sonyc-project/SONYC-Home/Hardware/Design Files/STEP files/Gasket rev2.STEP

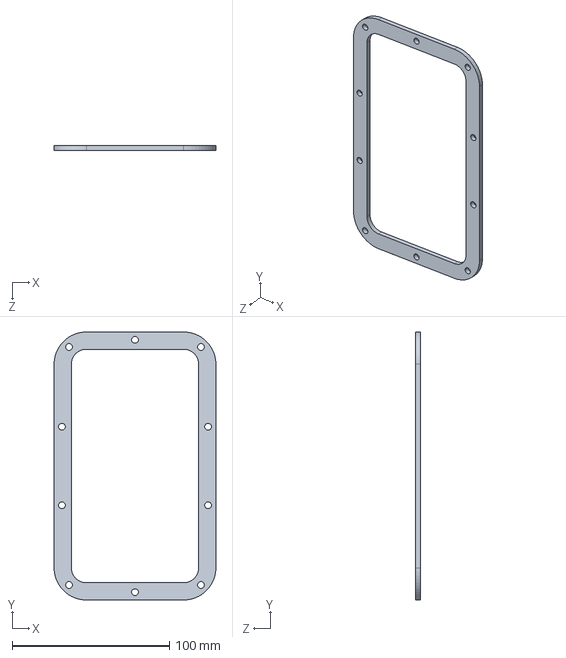
[picture p9: CAD file, 2023-06-01]
Hardware/Design Files/STEP files/Gasket rev2.STEP
102.9 x 170.4 x 3.17 mm
