sonyc-project/SONYC-Home/Hardware/Design Files/Solidworks CAD/SONYC-SW-database/SHR-05V-S-B.sldprt

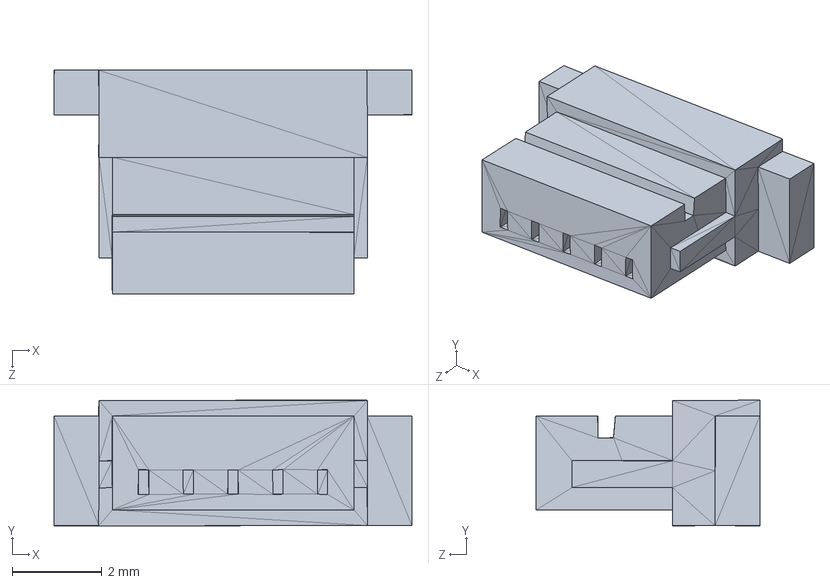
[picture p10: CAD file, 2023-06-01]
Hardware/Design Files/Solidworks CAD/SONYC-SW-database/SHR-05V-S-B.sldprt
8.00 x 2.81 x 5.01 mm
