sonyc-project/SONYC-Home/Hardware/Design Files/Solidworks CAD/SONYC-SW-database/Back-Plate.SLDPRT

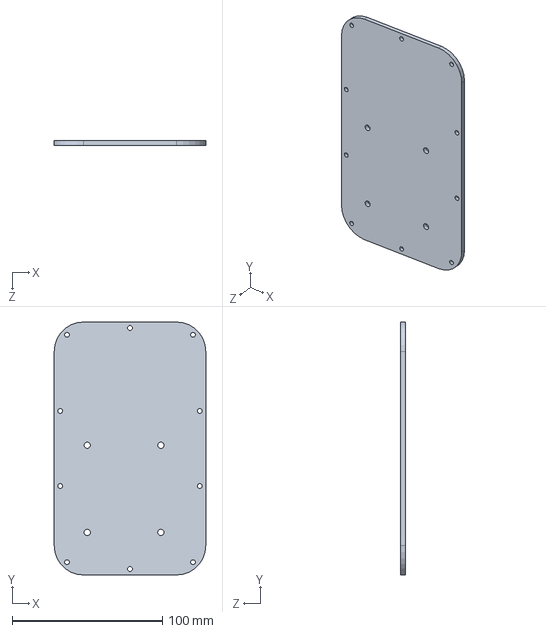
[picture p11: CAD file, 2023-06-01]
Hardware/Design Files/Solidworks CAD/SONYC-SW-database/Back-Plate.SLDPRT
100.9 x 168.4 x 3.00 mm
