sonyc-project/SONYC-Home/Hardware/Design Files/Solidworks CAD/SONYC-SW-database/cicoil-cable.SLDPRT

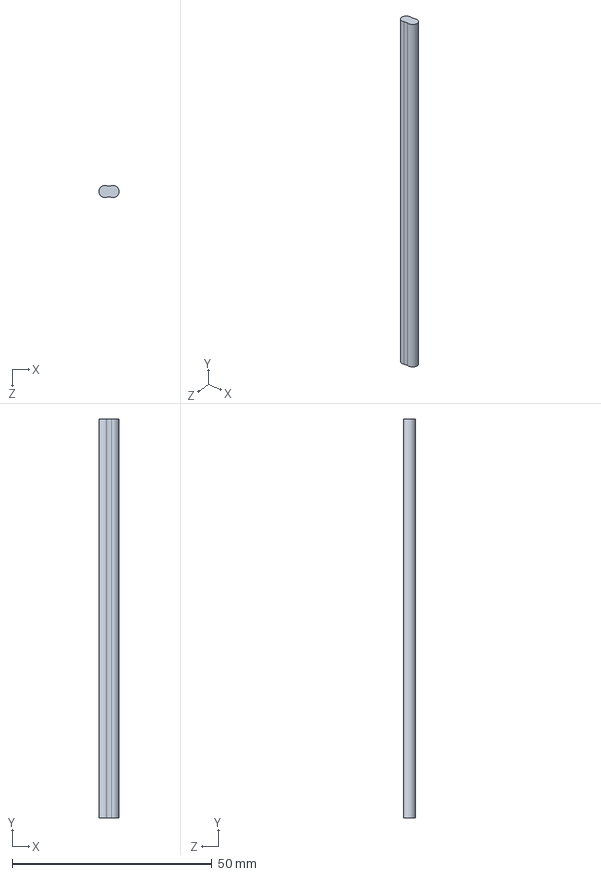
[picture p12: CAD file, 2023-06-01]
Hardware/Design Files/Solidworks CAD/SONYC-SW-database/cicoil-cable.SLDPRT
5.06 x 100.0 x 3.05 mm
