sonyc-project/SONYC-Home/Hardware/Design Files/Solidworks CAD/SONYC-SW-database/SONYC-Heat-sink-block.SLDPRT

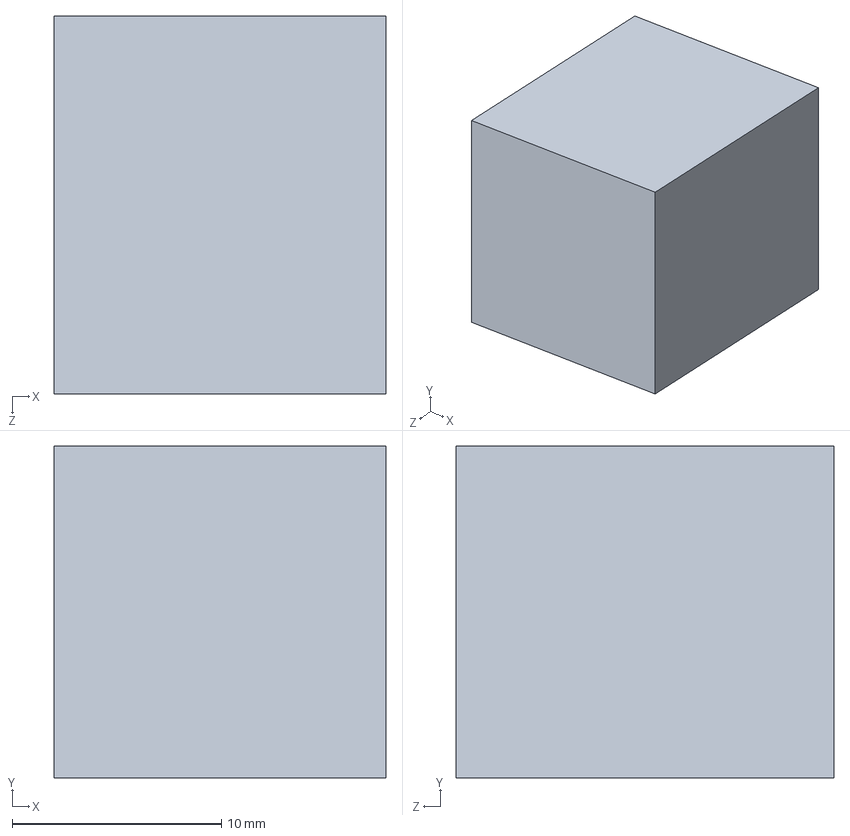
[picture p13: CAD file, 2023-06-01]
Hardware/Design Files/Solidworks CAD/SONYC-SW-database/SONYC-Heat-sink-block.SLDPRT
15.9 x 15.9 x 18.1 mm
