sonyc-project/SONYC-Home/Hardware/History/Assembly Photos/Image from iOS (94).jpg

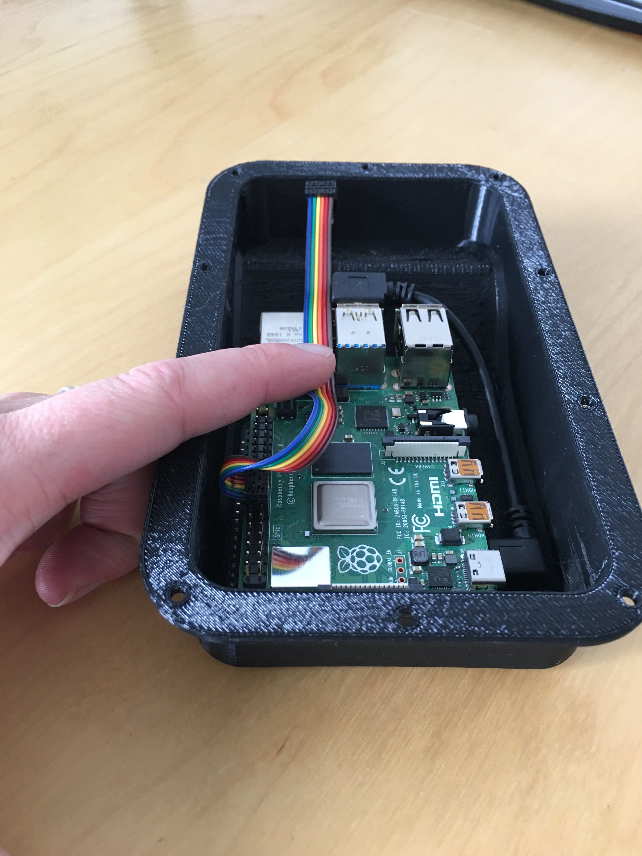
Hardware/History/Assembly Photos/Image from iOS (94).jpg
