sonyc-project/SONYC-Home/Hardware/History/Assembly Photos/Image from iOS (95).jpg

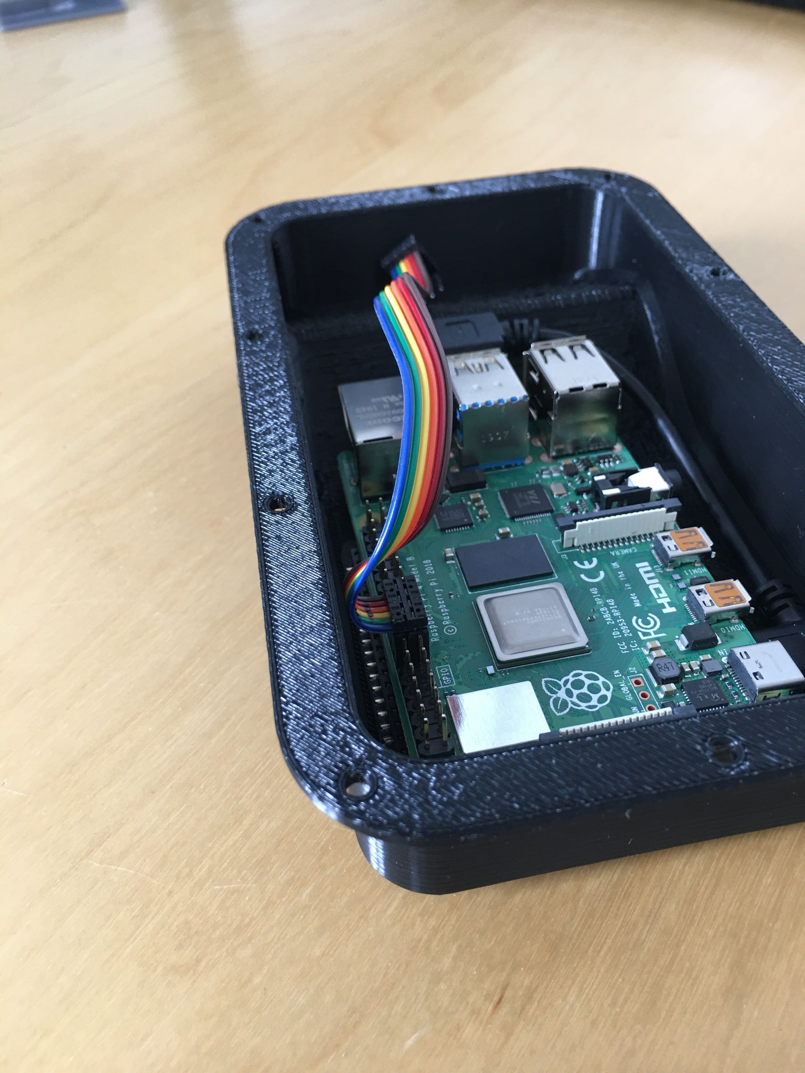
Hardware/History/Assembly Photos/Image from iOS (95).jpg
