sonyc-project/SONYC-Home/Hardware/History/Assembly Photos/Image from iOS (96).jpg

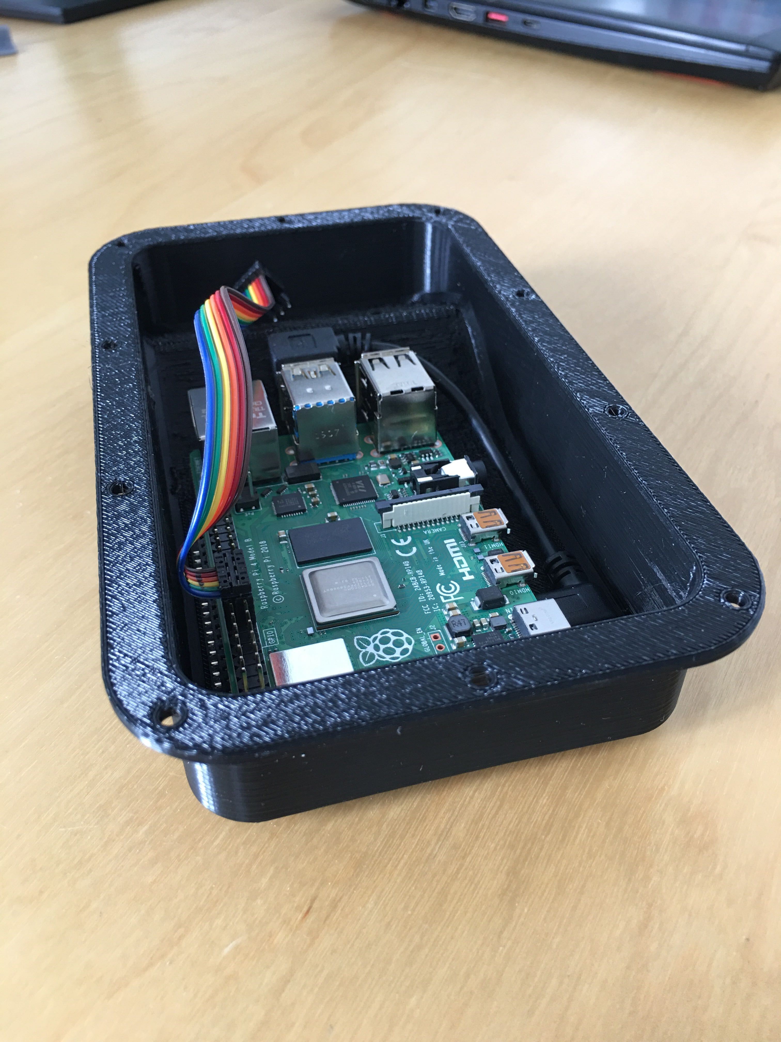
Hardware/History/Assembly Photos/Image from iOS (96).jpg
