sonyc-project/SONYC-Home/Hardware/History/Assembly Photos/Image from iOS (97).jpg

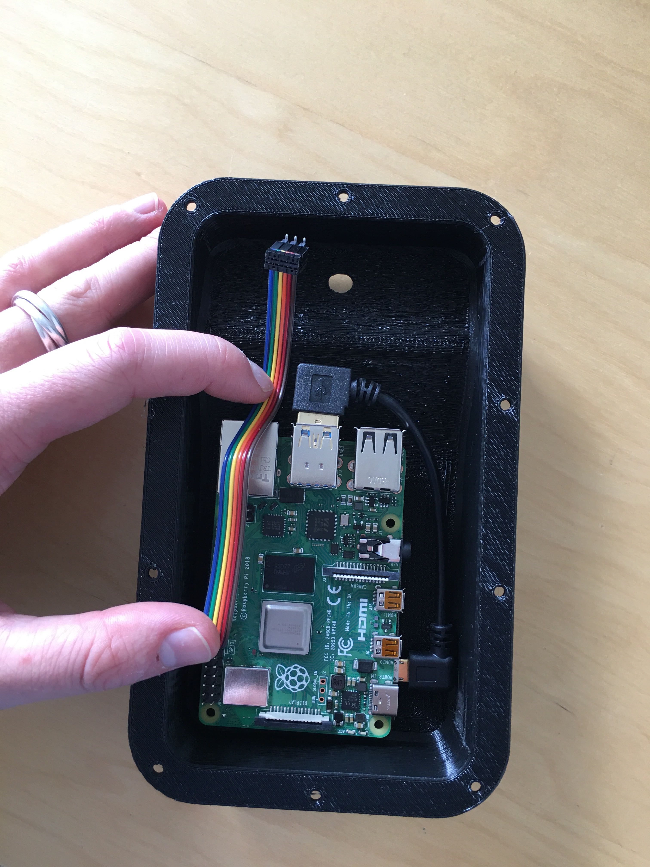
Hardware/History/Assembly Photos/Image from iOS (97).jpg
