sonyc-project/SONYC-Home/Hardware/History/Assembly Photos/Image from iOS (98).jpg

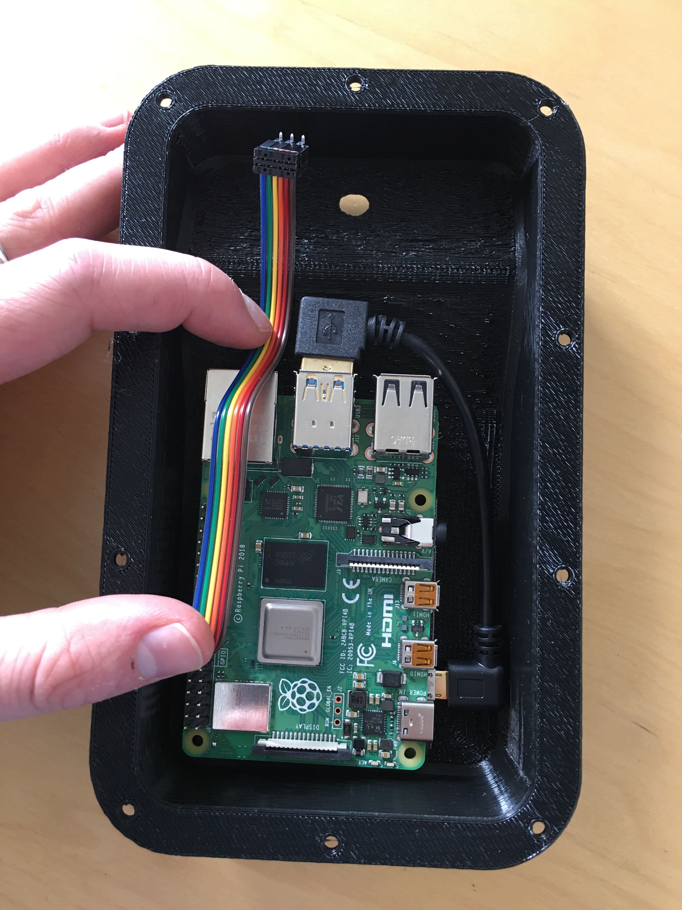
Hardware/History/Assembly Photos/Image from iOS (98).jpg
