sonyc-project/SONYC-Home/Hardware/History/Assembly Photos/Image from iOS (161).jpg

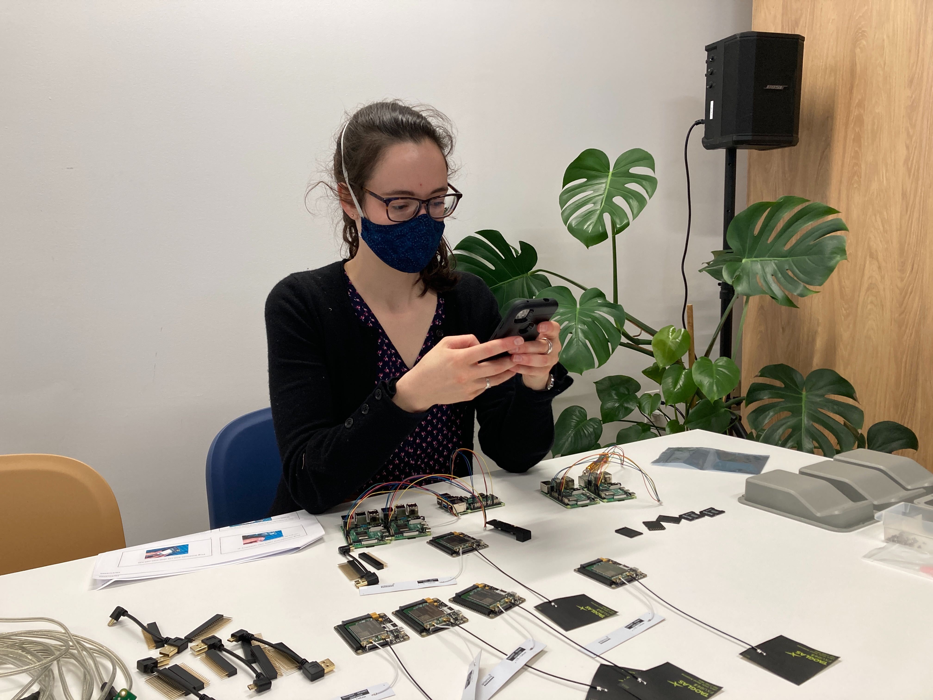
Hardware/History/Assembly Photos/Image from iOS (161).jpg
