sonyc-project/SONYC-Home/Hardware/History/Assembly Photos/Image from iOS (162).jpg

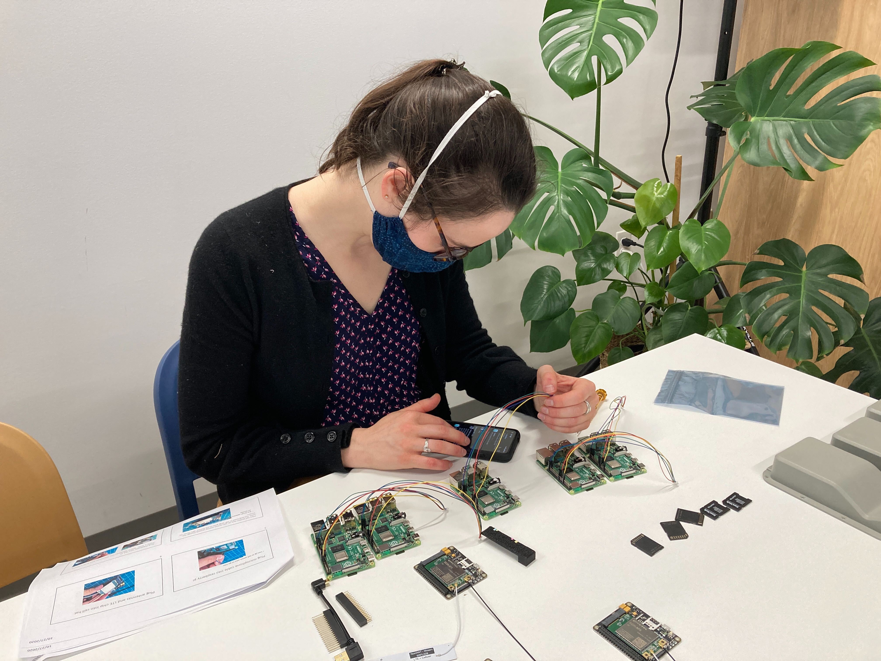
Hardware/History/Assembly Photos/Image from iOS (162).jpg
