sonyc-project/SONYC-Home/Hardware/History/Assembly Photos/Image from iOS (163).jpg

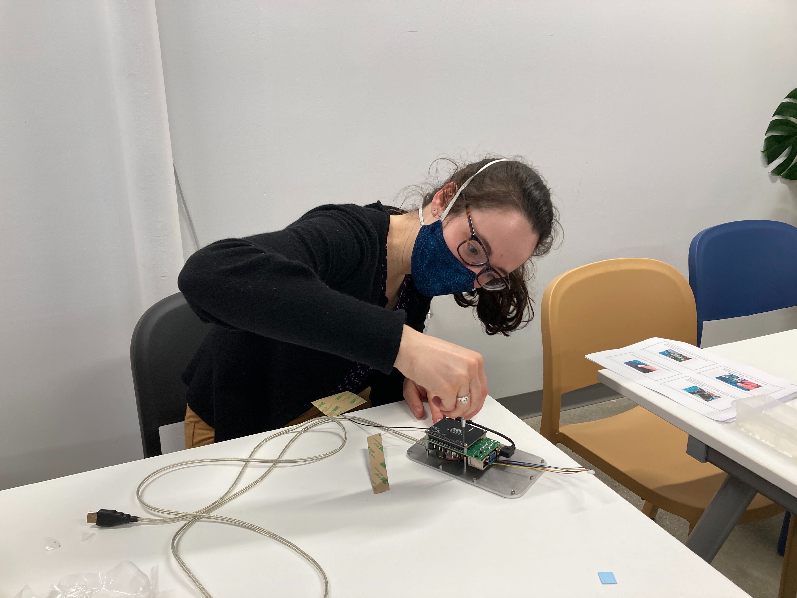
Hardware/History/Assembly Photos/Image from iOS (163).jpg
