sonyc-project/SONYC-Home/Hardware/History/Assembly Photos/Image from iOS (164).jpg

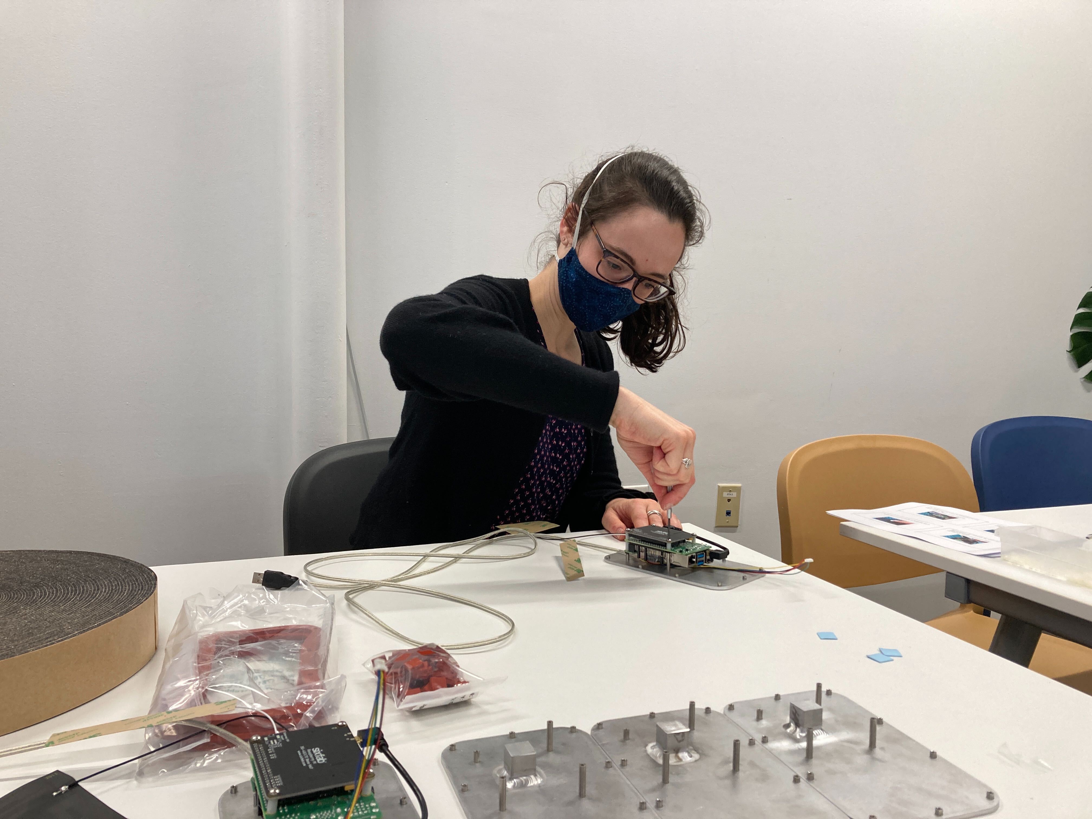
Hardware/History/Assembly Photos/Image from iOS (164).jpg
