sonyc-project/SONYC-Home/Hardware/History/Assembly Photos/Image from iOS (165) (1).jpg

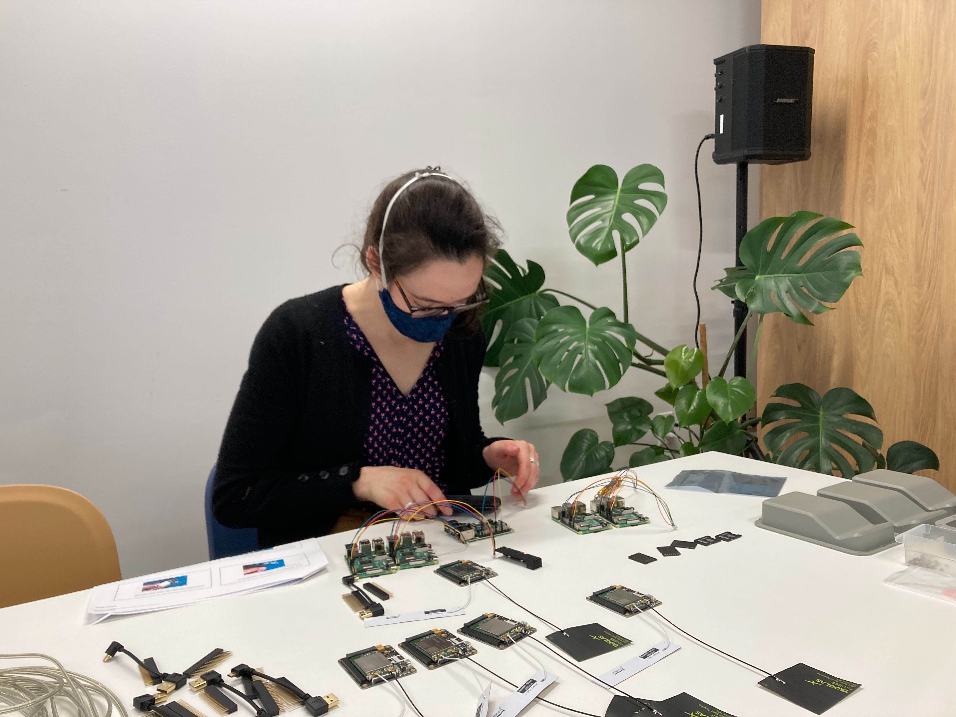
Hardware/History/Assembly Photos/Image from iOS (165) (1).jpg
