sonyc-project/SONYC-Home/Hardware/History/Assembly Photos/IMG_3658.jpeg

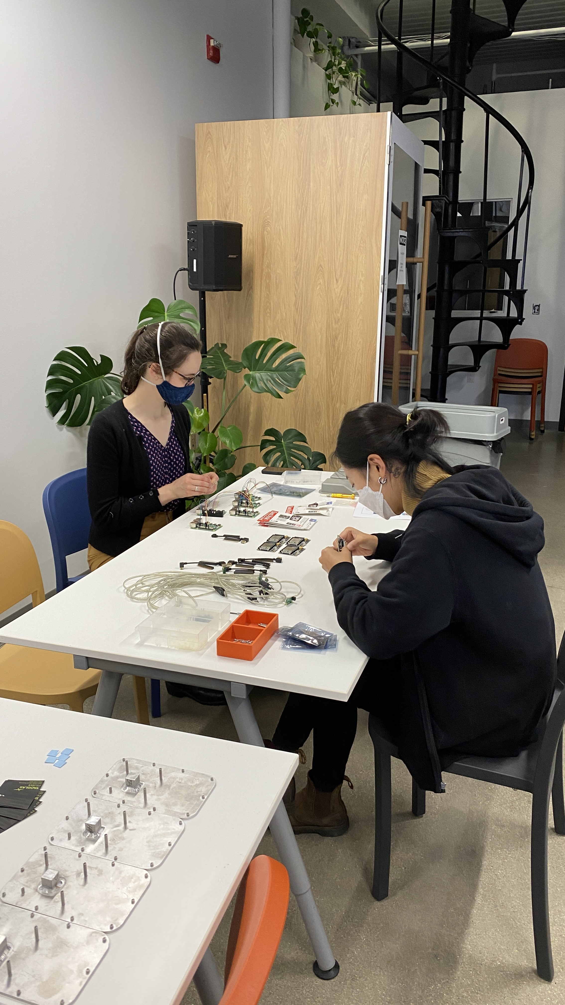
Hardware/History/Assembly Photos/IMG_3658.jpeg
