sonyc-project/SONYC-Home/Hardware/History/Assembly Photos/IMG_3659.jpeg

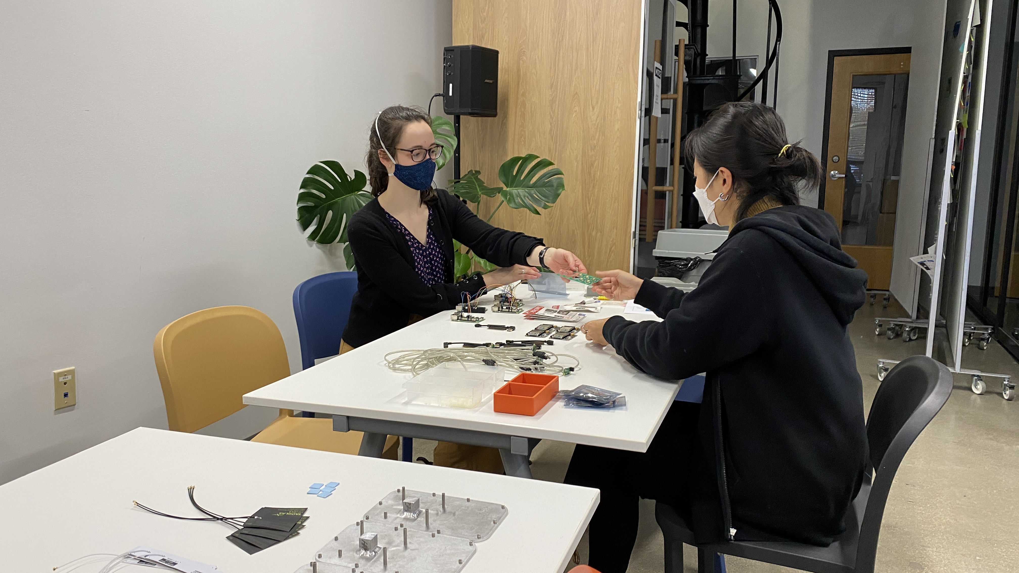
Hardware/History/Assembly Photos/IMG_3659.jpeg
