sonyc-project/SONYC-Home/Hardware/History/Assembly Photos/IMG_3662.jpeg

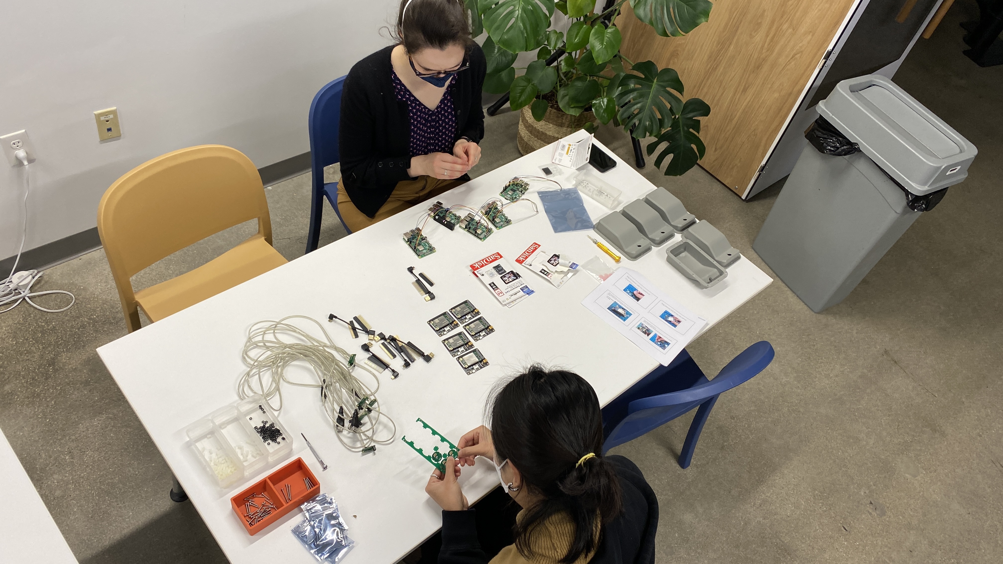
Hardware/History/Assembly Photos/IMG_3662.jpeg
