sonyc-project/SONYC-Home/Hardware/History/Assembly Photos/IMG_3663.jpeg

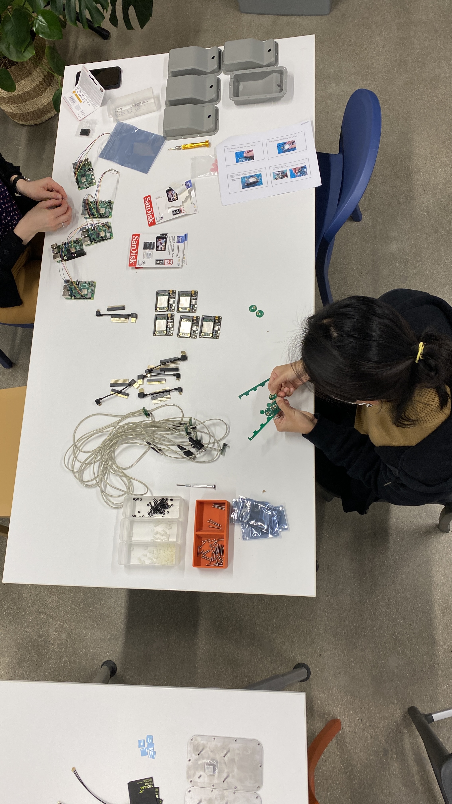
Hardware/History/Assembly Photos/IMG_3663.jpeg
