sonyc-project/SONYC-Home/Hardware/History/Assembly Photos/IMG_3664.jpeg

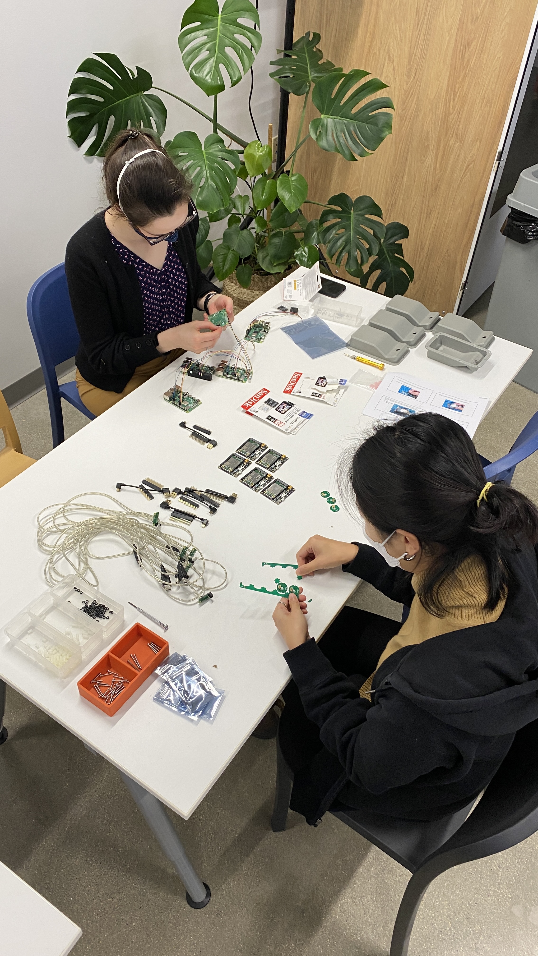
Hardware/History/Assembly Photos/IMG_3664.jpeg
