sonyc-project/SONYC-Home/Hardware/History/Assembly Photos/IMG_3665.jpeg

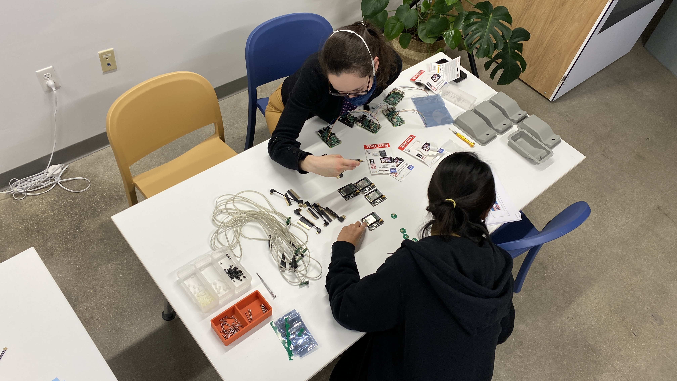
Hardware/History/Assembly Photos/IMG_3665.jpeg
