sonyc-project/SONYC-Home/Hardware/History/Assembly Photos/IMG_3666.jpeg

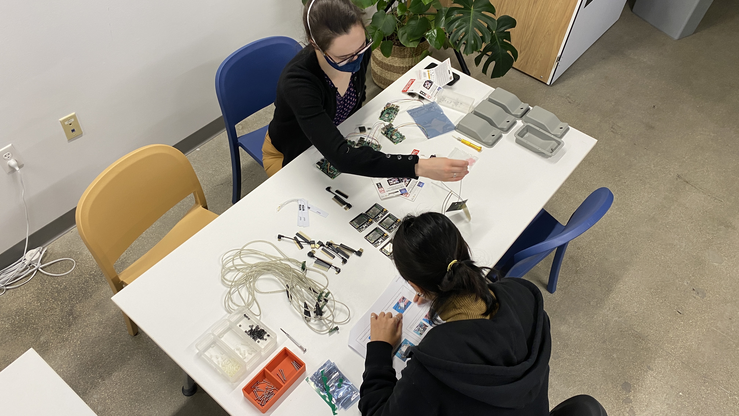
Hardware/History/Assembly Photos/IMG_3666.jpeg
