sonyc-project/SONYC-Home/Hardware/History/Assembly Photos/IMG_3667.jpeg

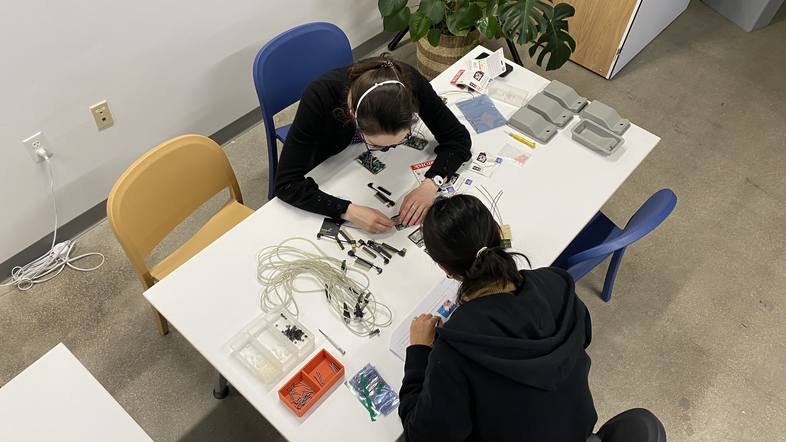
Hardware/History/Assembly Photos/IMG_3667.jpeg
