sonyc-project/SONYC-Home/Hardware/History/Assembly Photos/IMG_3668.jpeg

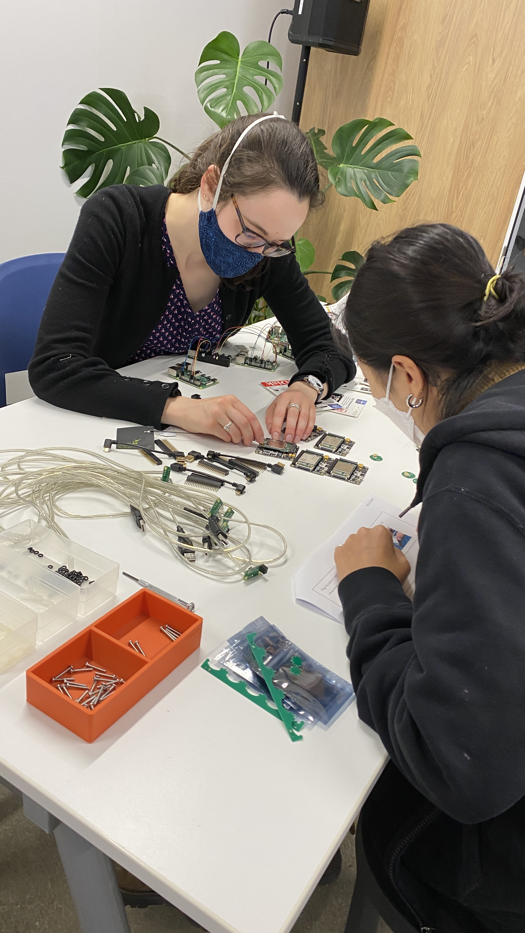
Hardware/History/Assembly Photos/IMG_3668.jpeg
