sonyc-project/SONYC-Home/Hardware/History/Assembly Photos/IMG_3672.jpeg

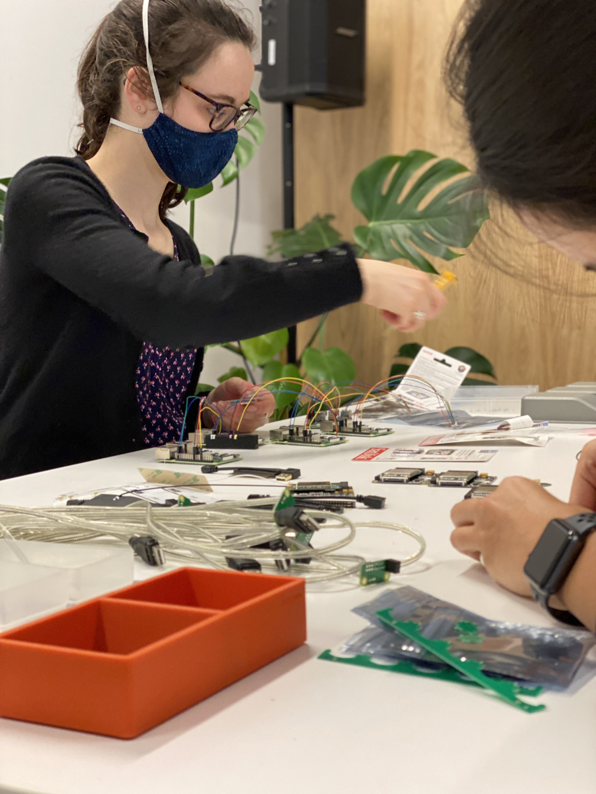
Hardware/History/Assembly Photos/IMG_3672.jpeg
