sonyc-project/SONYC-Home/Hardware/History/Assembly Photos/IMG_3977.JPG

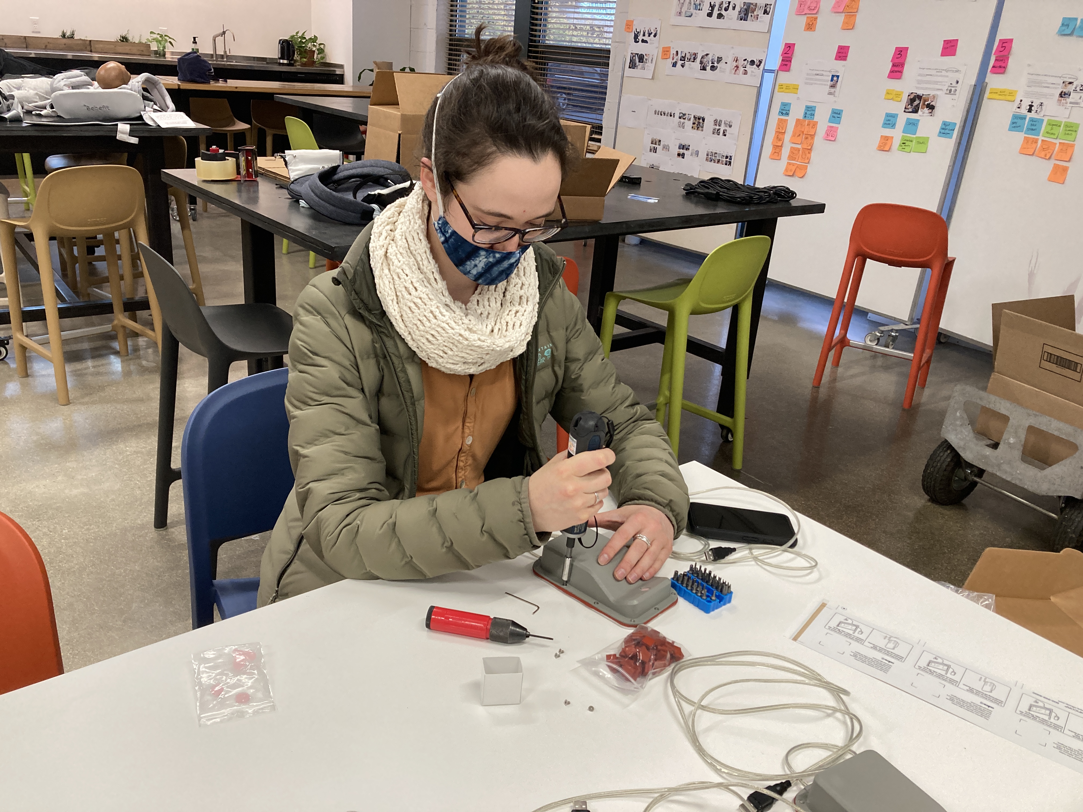
Hardware/History/Assembly Photos/IMG_3977.JPG
