sonyc-project/SONYC-Home/Hardware/History/Assembly Photos/IMG_3978.JPG

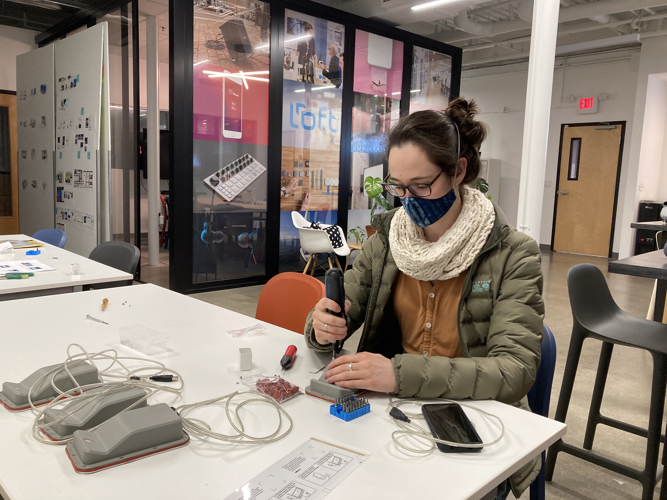
Hardware/History/Assembly Photos/IMG_3978.JPG
