sonyc-project/SONYC-Home/Hardware/History/Assembly Photos/IMG_3979.JPG

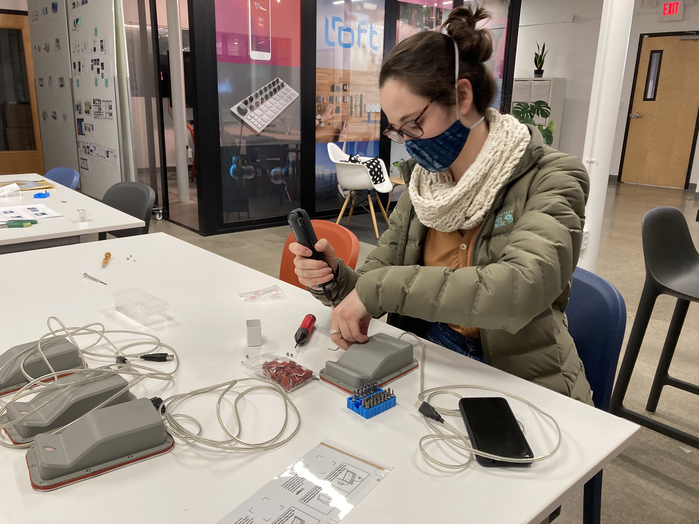
Hardware/History/Assembly Photos/IMG_3979.JPG
