sonyc-project/SONYC-Home/Hardware/History/Assembly Photos/IMG_3980.JPG

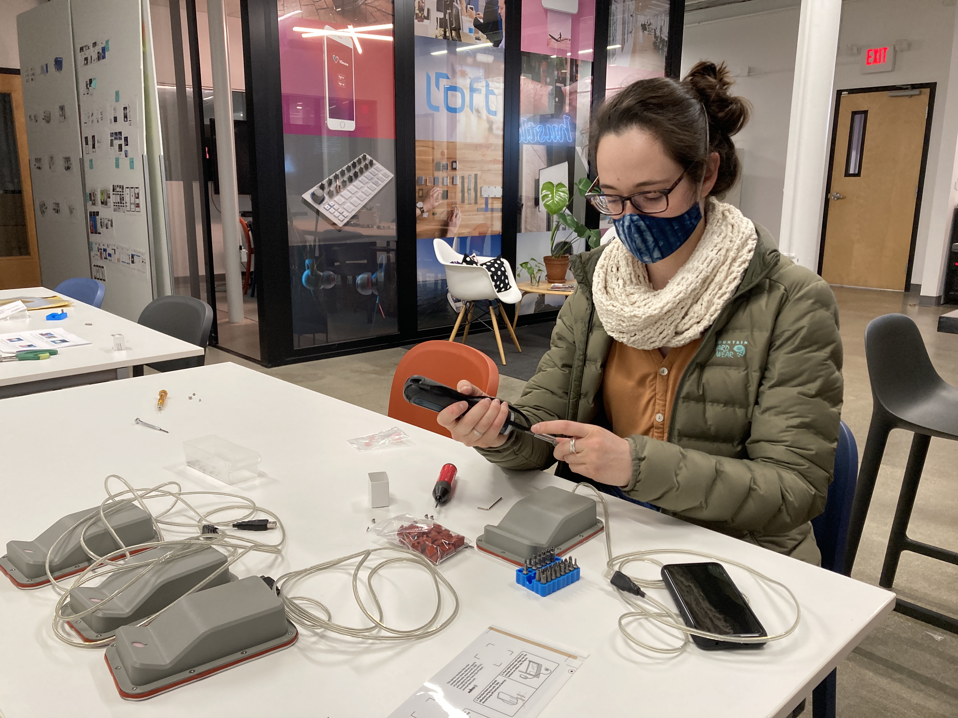
Hardware/History/Assembly Photos/IMG_3980.JPG
