sonyc-project/SONYC-Home/Hardware/History/Assembly Photos/IMG_3981.JPG

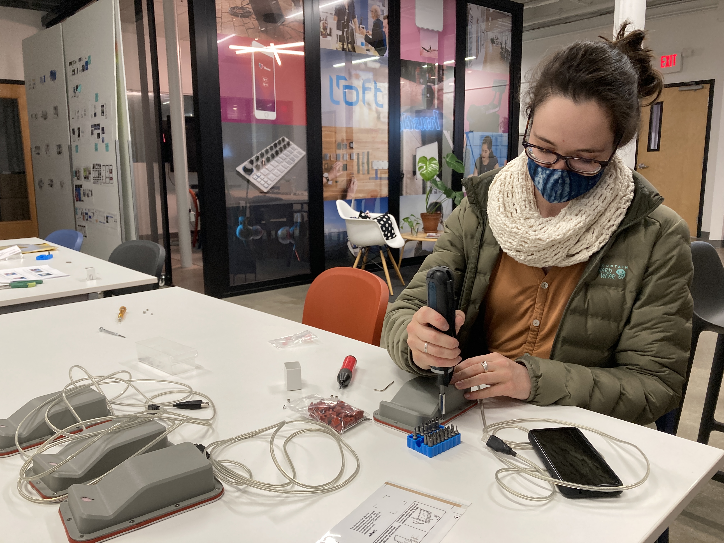
Hardware/History/Assembly Photos/IMG_3981.JPG
