sonyc-project/SONYC-Home/Hardware/History/Assembly Photos/IMG_3982.JPG

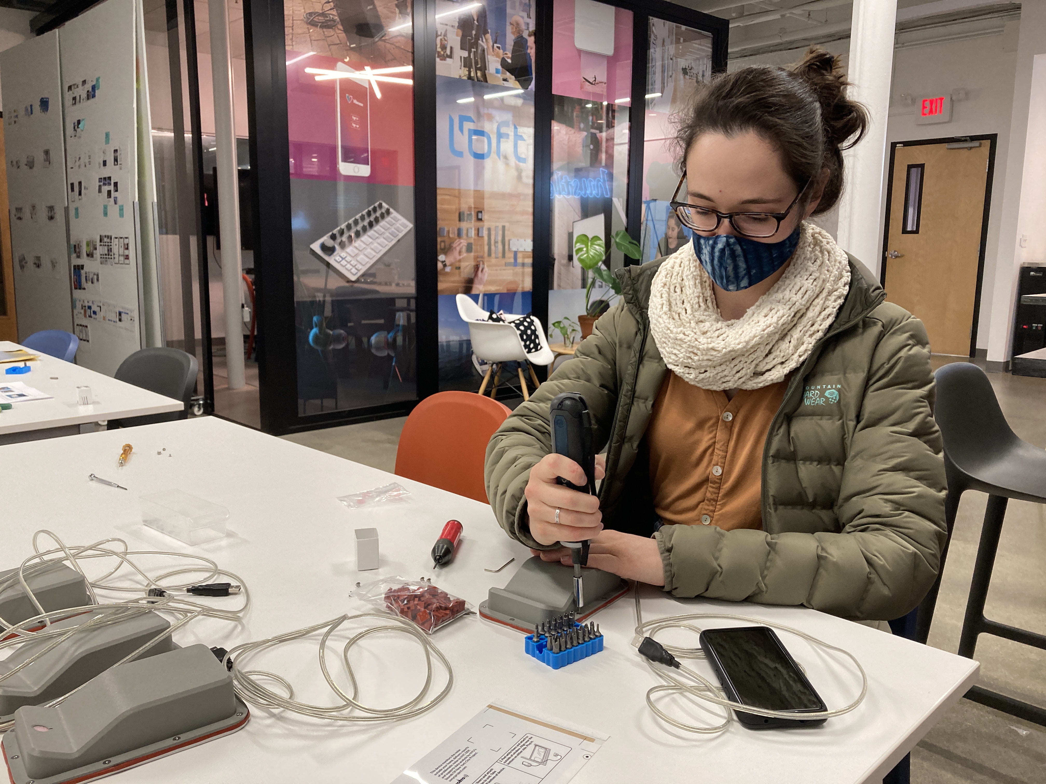
Hardware/History/Assembly Photos/IMG_3982.JPG
