sonyc-project/SONYC-Home/Hardware/History/Assembly Photos/IMG_3983.JPG

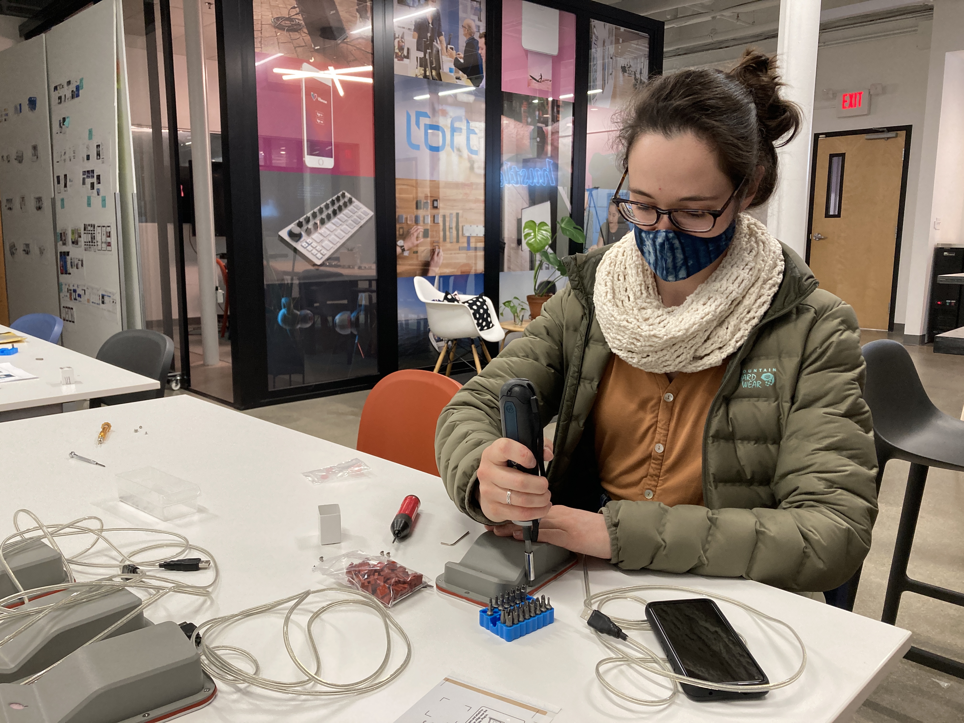
Hardware/History/Assembly Photos/IMG_3983.JPG
