sonyc-project/SONYC-Home/Hardware/History/Assembly Photos/IMG_3984.JPG

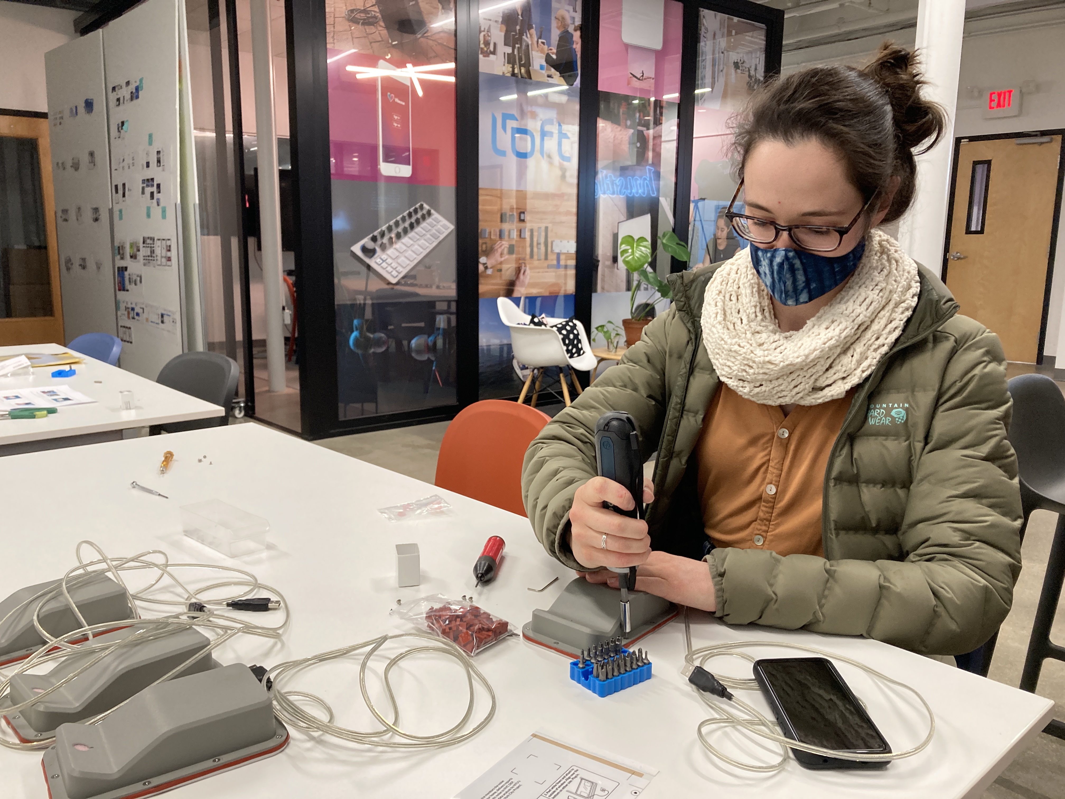
Hardware/History/Assembly Photos/IMG_3984.JPG
