sonyc-project/SONYC-Home/Hardware/History/Assembly Photos/IMG_3985.JPG

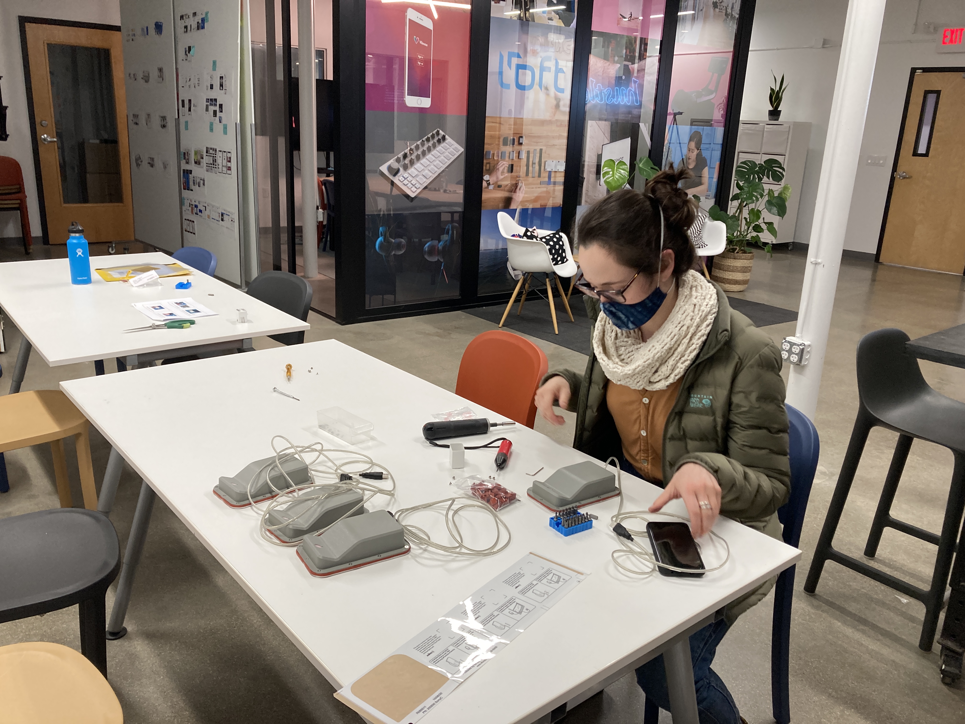
Hardware/History/Assembly Photos/IMG_3985.JPG
