sonyc-project/SONYC-Home/Hardware/History/Assembly Photos/IMG_3986.JPG

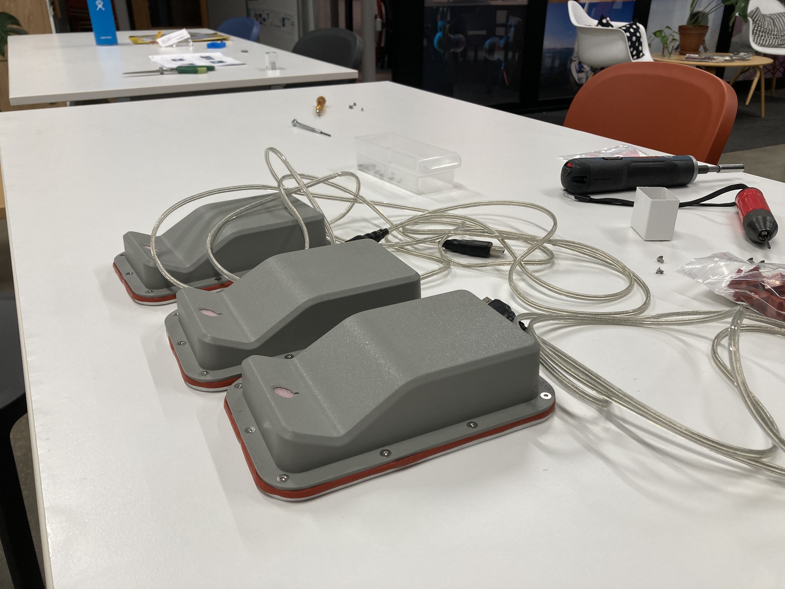
Hardware/History/Assembly Photos/IMG_3986.JPG
