sonyc-project/SONYC-Home/Hardware/History/Assembly Photos/IMG_20201028_170915_01.jpg

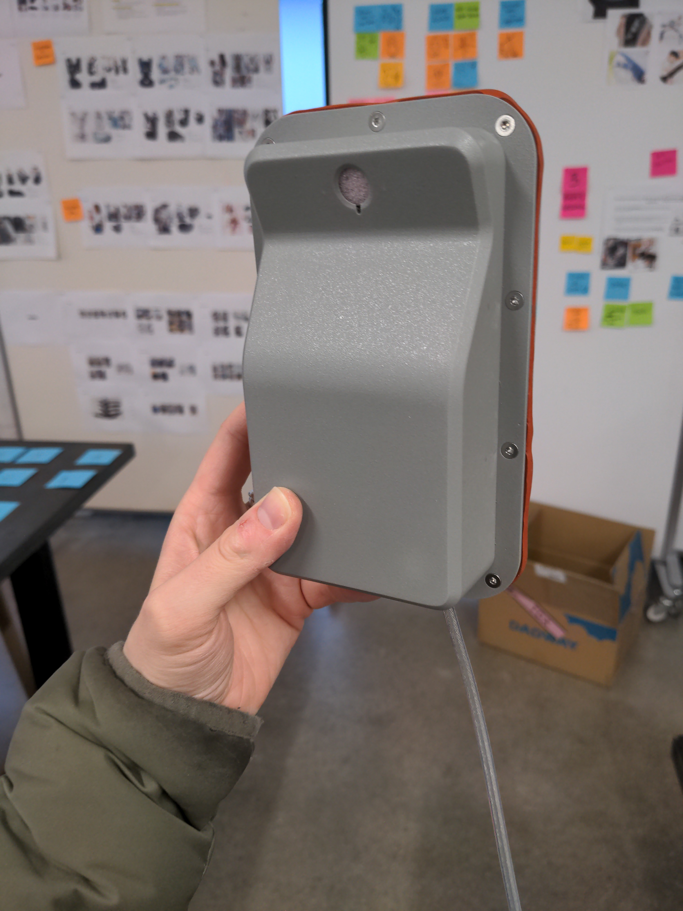
Hardware/History/Assembly Photos/IMG_20201028_170915_01.jpg
