sonyc-project/SONYC-Home/Hardware/History/Assembly Photos/PXL_20201026_215932497~2.jpg

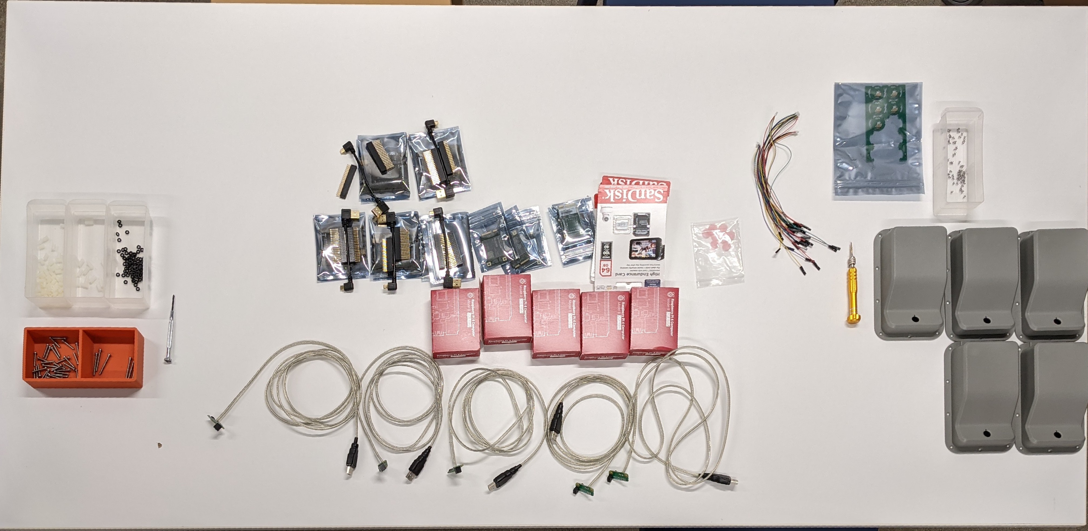
Hardware/History/Assembly Photos/PXL_20201026_215932497~2.jpg
