sonyc-project/SONYC-Home/Hardware/History/Assembly Photos/PXL_20201026_220055273.jpg

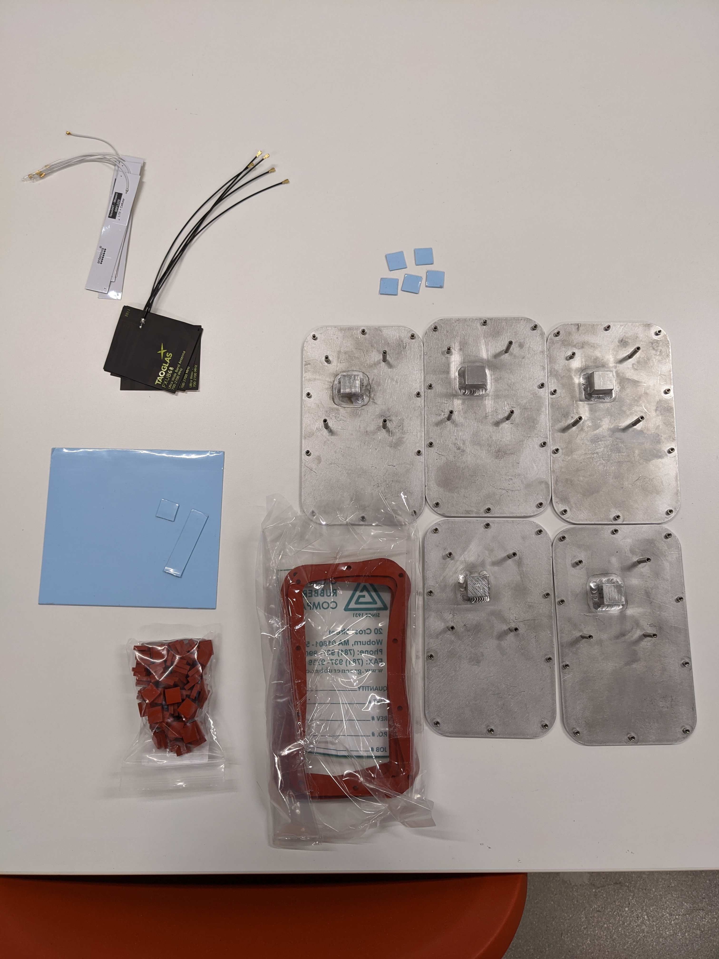
Hardware/History/Assembly Photos/PXL_20201026_220055273.jpg
