sonyc-project/SONYC-Home/Hardware/History/Assembly Photos/PXL_20201026_220131812.jpg

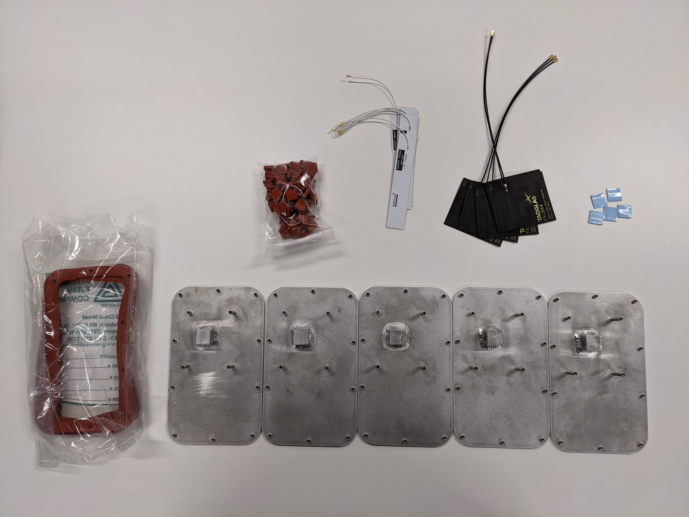
Hardware/History/Assembly Photos/PXL_20201026_220131812.jpg
