sonyc-project/SONYC-Home/Hardware/History/Assembly Photos/PXL_20201026_220134488.jpg

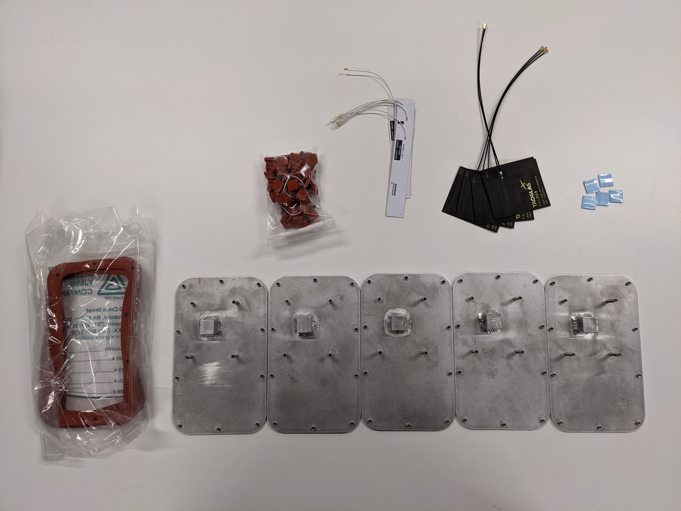
Hardware/History/Assembly Photos/PXL_20201026_220134488.jpg
