sonyc-project/SONYC-Home/Hardware/History/Assembly Photos/PXL_20201026_220347487.jpg

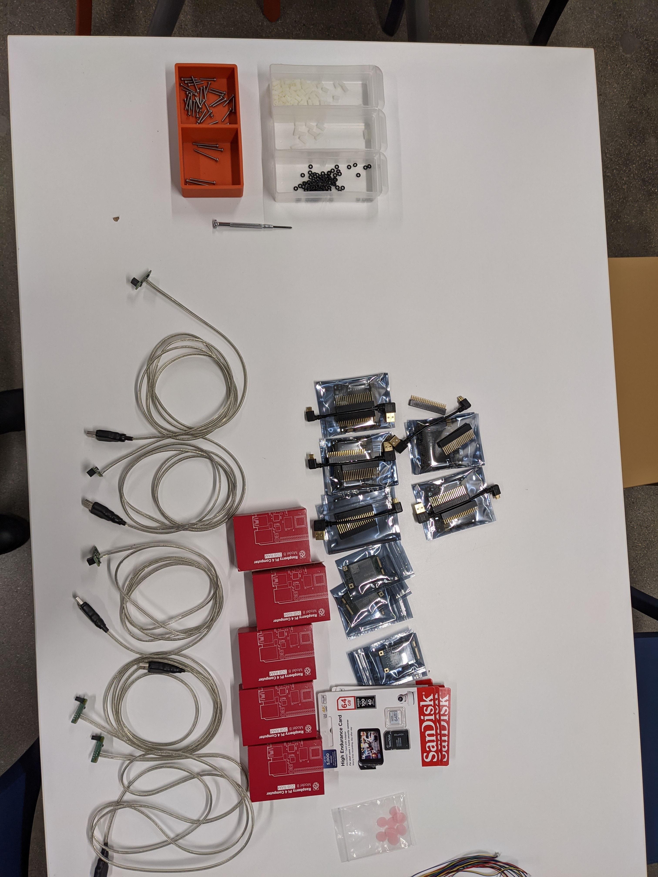
Hardware/History/Assembly Photos/PXL_20201026_220347487.jpg
