sonyc-project/SONYC-Home/Hardware/History/Assembly Photos/PXL_20201027_130116804.jpg

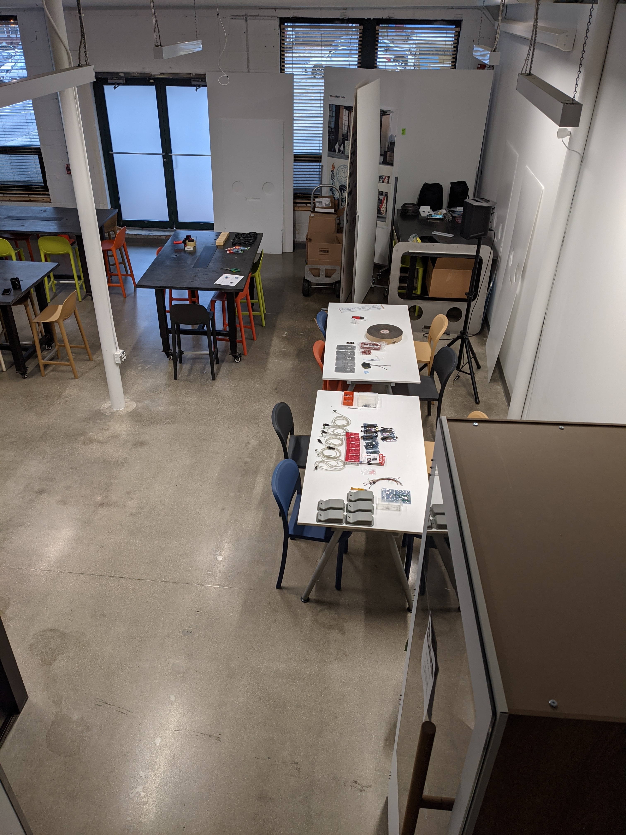
Hardware/History/Assembly Photos/PXL_20201027_130116804.jpg
