sonyc-project/SONYC-Home/Hardware/History/Assembly Photos/PXL_20201027_130131755.jpg

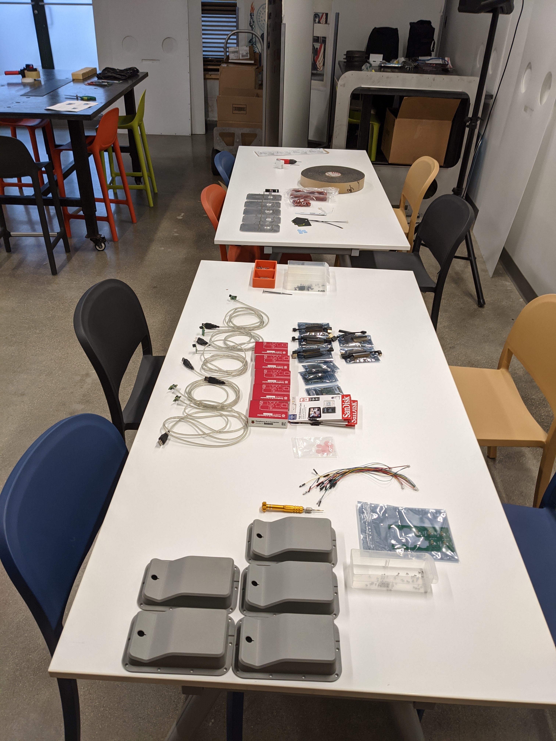
Hardware/History/Assembly Photos/PXL_20201027_130131755.jpg
