sonyc-project/SONYC-Home/Hardware/History/Assembly Photos/PXL_20201027_130139757.jpg

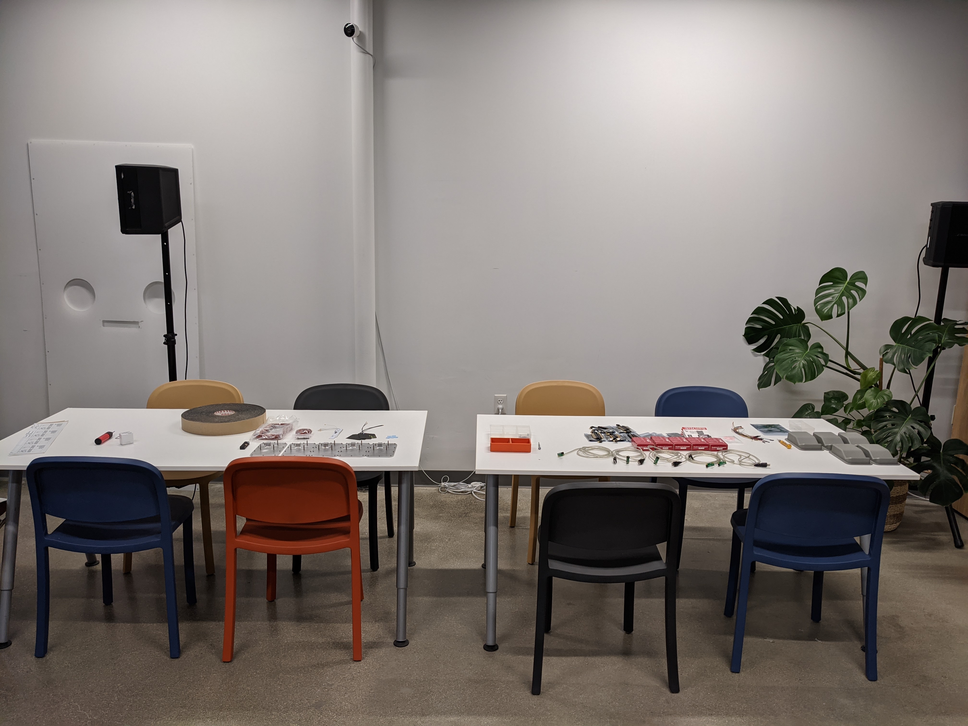
Hardware/History/Assembly Photos/PXL_20201027_130139757.jpg
