sonyc-project/SONYC-Home/Hardware/History/Assembly Photos/PXL_20201027_133501478.jpg

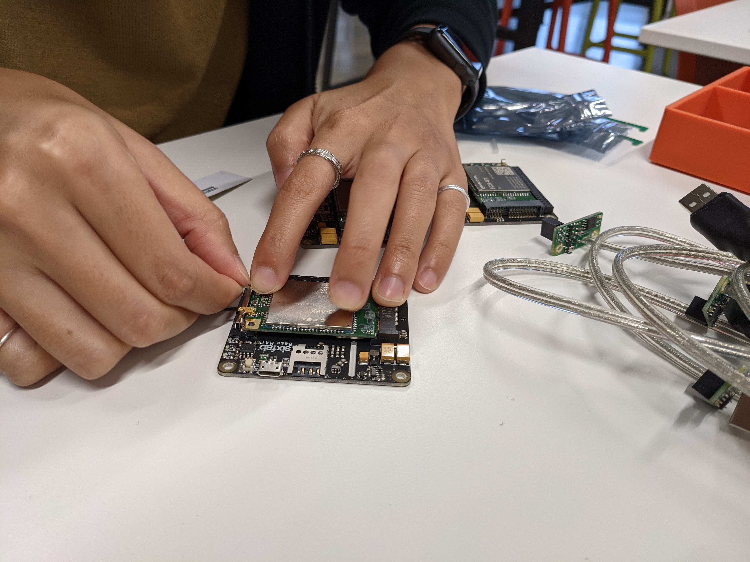
Hardware/History/Assembly Photos/PXL_20201027_133501478.jpg
