sonyc-project/SONYC-Home/Hardware/History/Assembly Photos/PXL_20201027_133505522.jpg

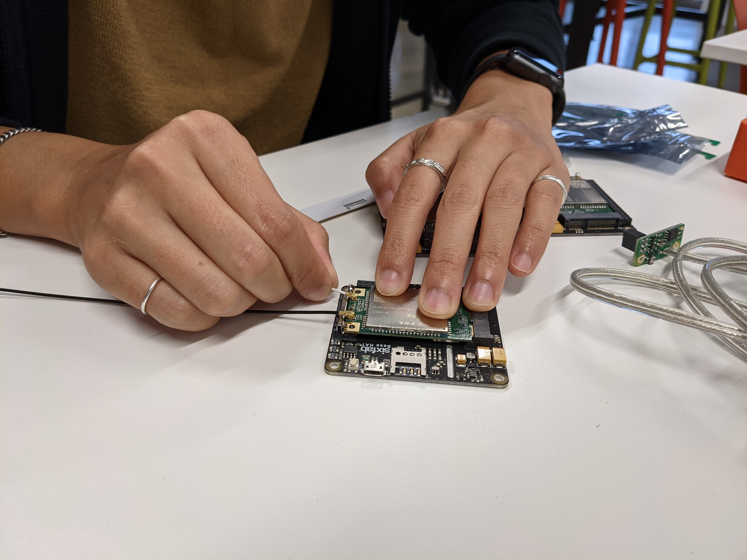
Hardware/History/Assembly Photos/PXL_20201027_133505522.jpg
