sonyc-project/SONYC-Home/Hardware/History/Assembly Photos/PXL_20201027_140714597.jpg

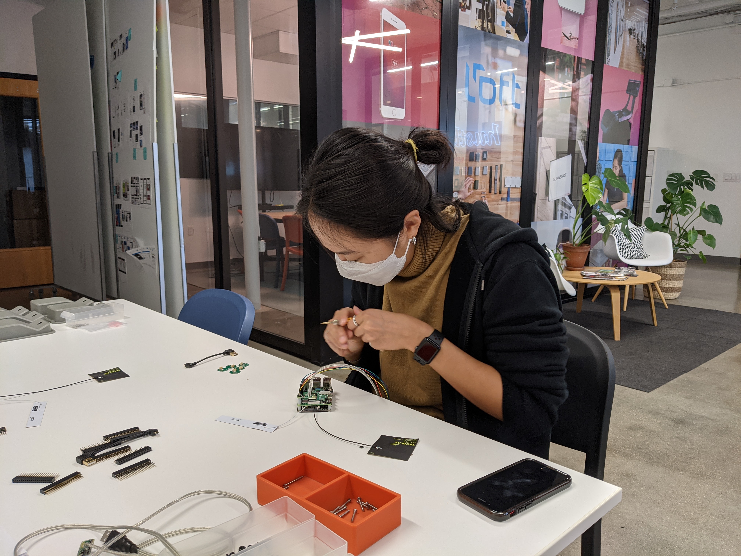
Hardware/History/Assembly Photos/PXL_20201027_140714597.jpg
