sonyc-project/SONYC-Home/Hardware/History/Assembly Photos/PXL_20201027_142332195.jpg

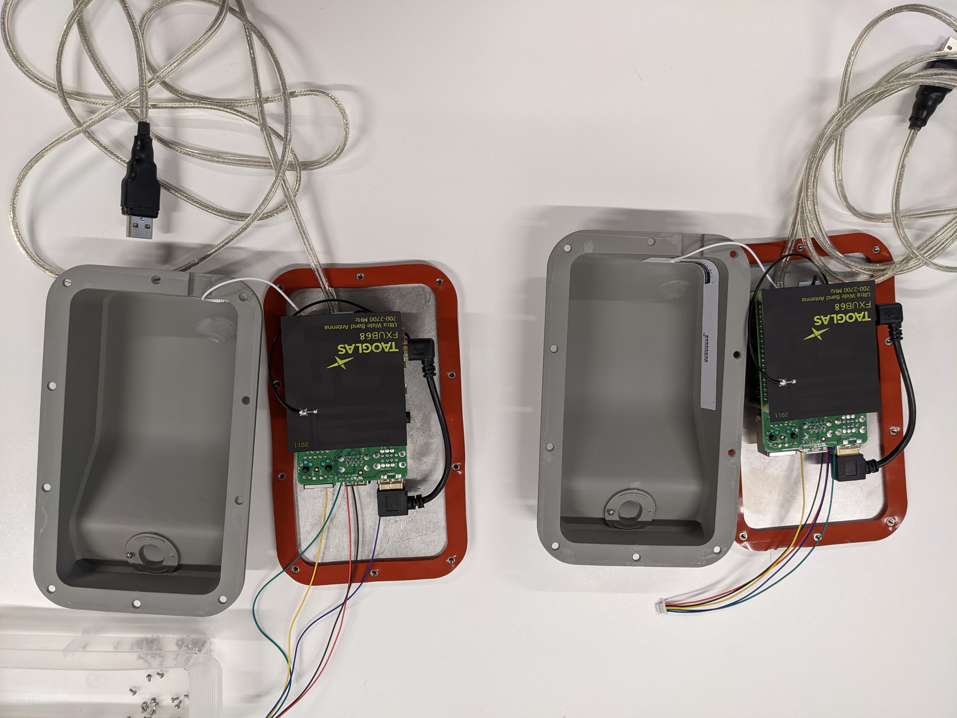
Hardware/History/Assembly Photos/PXL_20201027_142332195.jpg
