sonyc-project/SONYC-Home/Hardware/History/Assembly Photos/PXL_20201028_205749680.jpg

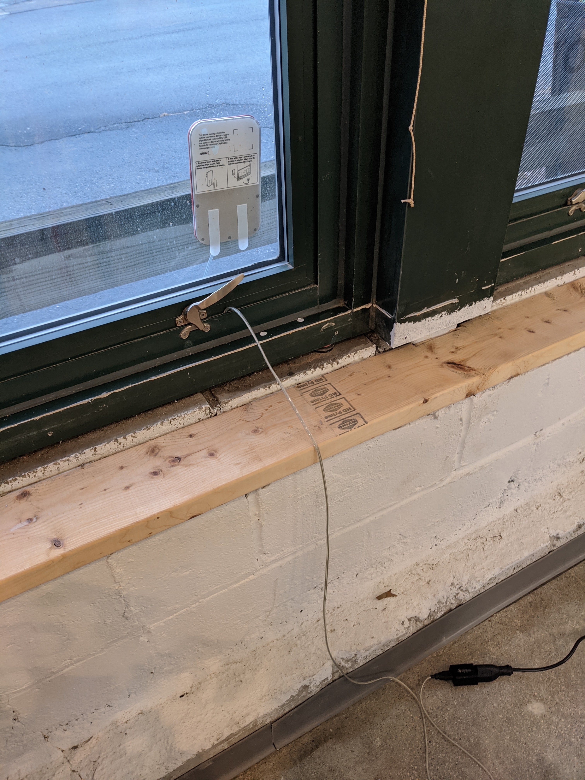
Hardware/History/Assembly Photos/PXL_20201028_205749680.jpg
