sonyc-project/SONYC-Home/Hardware/History/Assembly Photos/PXL_20201028_205756566.jpg

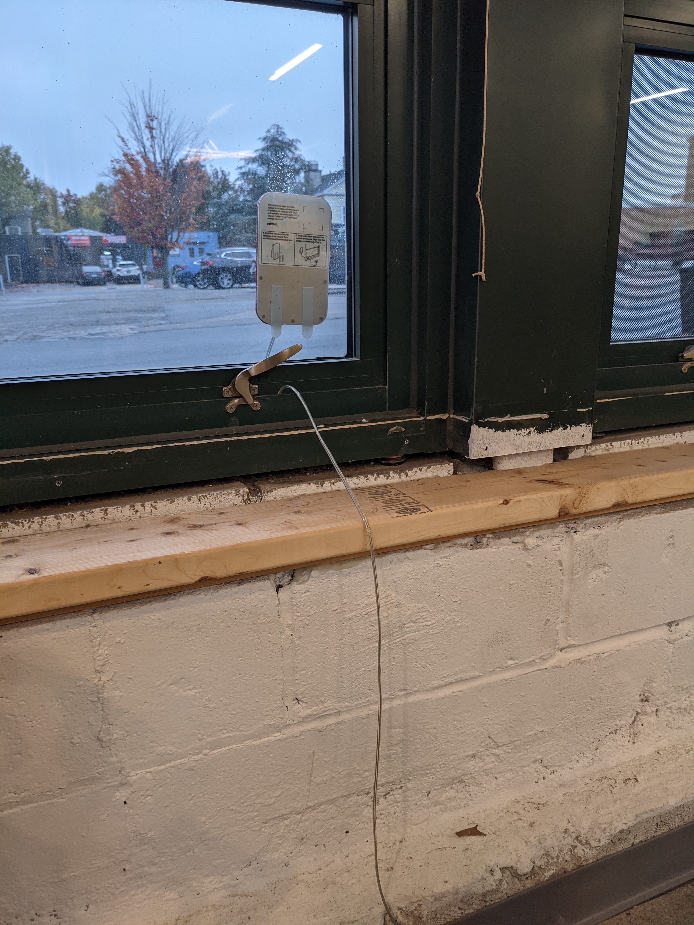
Hardware/History/Assembly Photos/PXL_20201028_205756566.jpg
