sonyc-project/SONYC-Home/Hardware/History/Assembly Photos/PXL_20201028_205809363.jpg

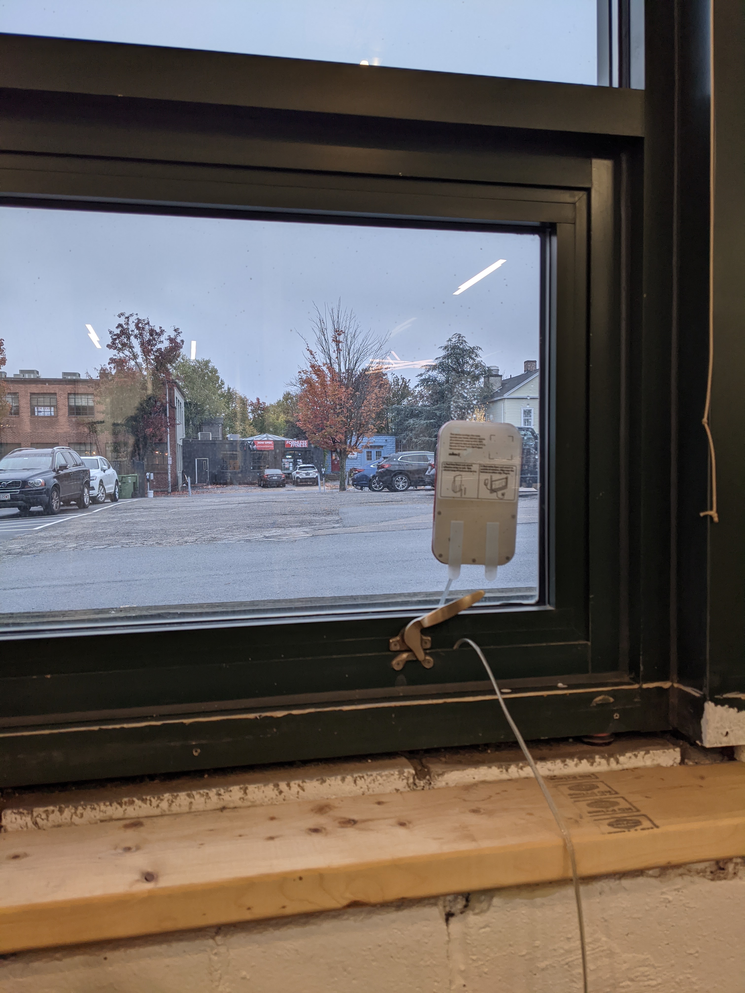
Hardware/History/Assembly Photos/PXL_20201028_205809363.jpg
