sonyc-project/SONYC-Home/Hardware/History/Assembly Photos/PXL_20201028_205831259.jpg

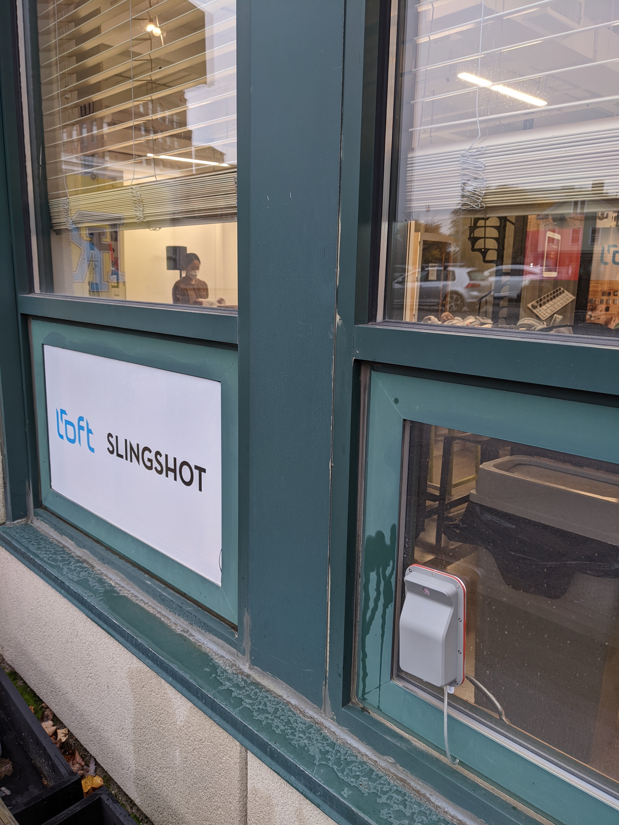
Hardware/History/Assembly Photos/PXL_20201028_205831259.jpg
