sonyc-project/SONYC-Home/Hardware/History/Assembly Photos/PXL_20201028_205844028.jpg

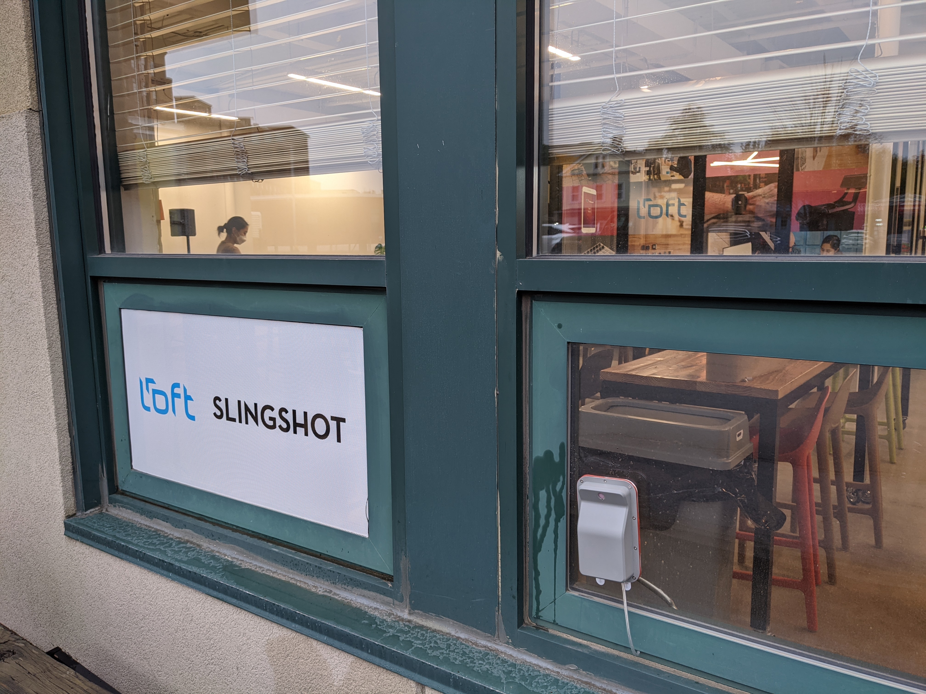
Hardware/History/Assembly Photos/PXL_20201028_205844028.jpg
