sonyc-project/SONYC-Home/Hardware/History/Assembly Photos/PXL_20201028_210826970.jpg

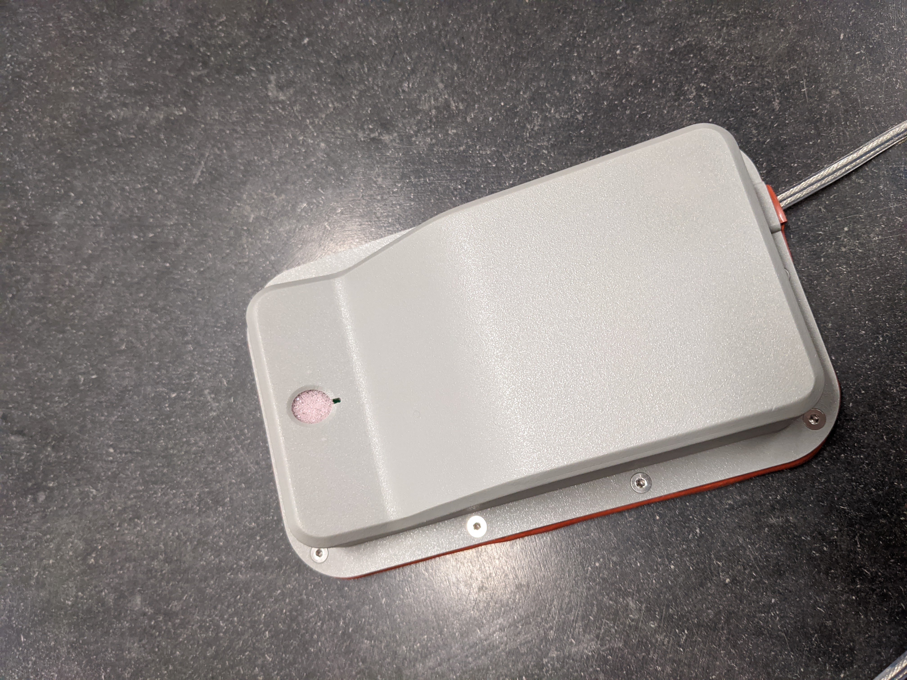
Hardware/History/Assembly Photos/PXL_20201028_210826970.jpg
