sonyc-project/SONYC-Home/Hardware/History/Assembly Photos/PXL_20201028_210834032.jpg

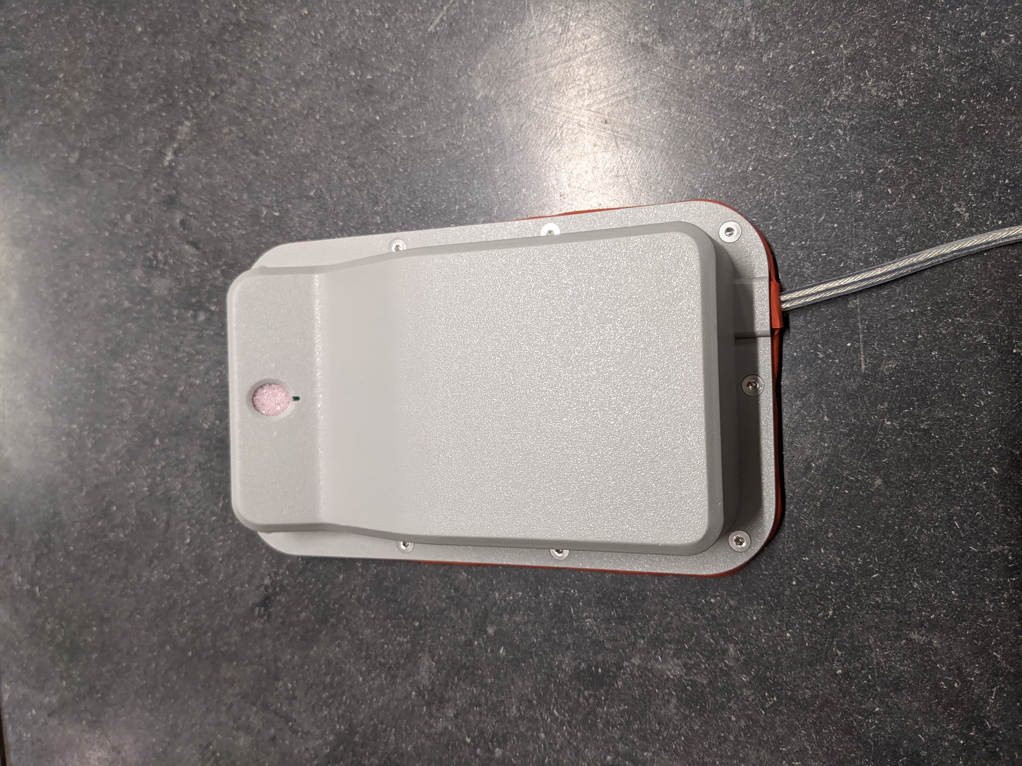
Hardware/History/Assembly Photos/PXL_20201028_210834032.jpg
