sonyc-project/SONYC-Home/Hardware/History/Assembly Photos/PXL_20201028_211617344.jpg

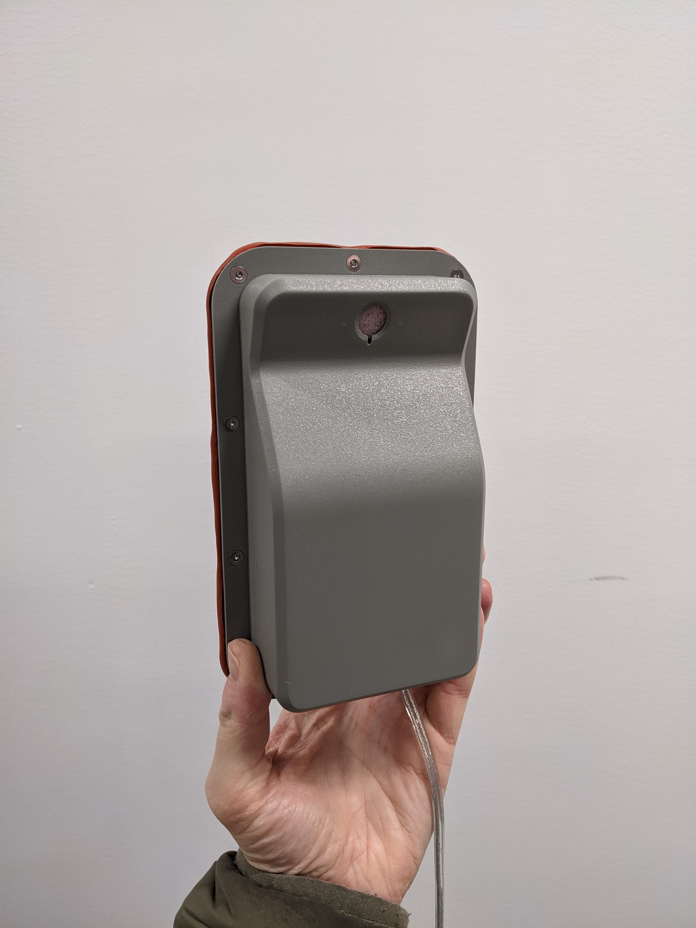
Hardware/History/Assembly Photos/PXL_20201028_211617344.jpg
