sonyc-project/SONYC-Home/Hardware/History/Assembly Photos/PXL_20201028_211705205.jpg

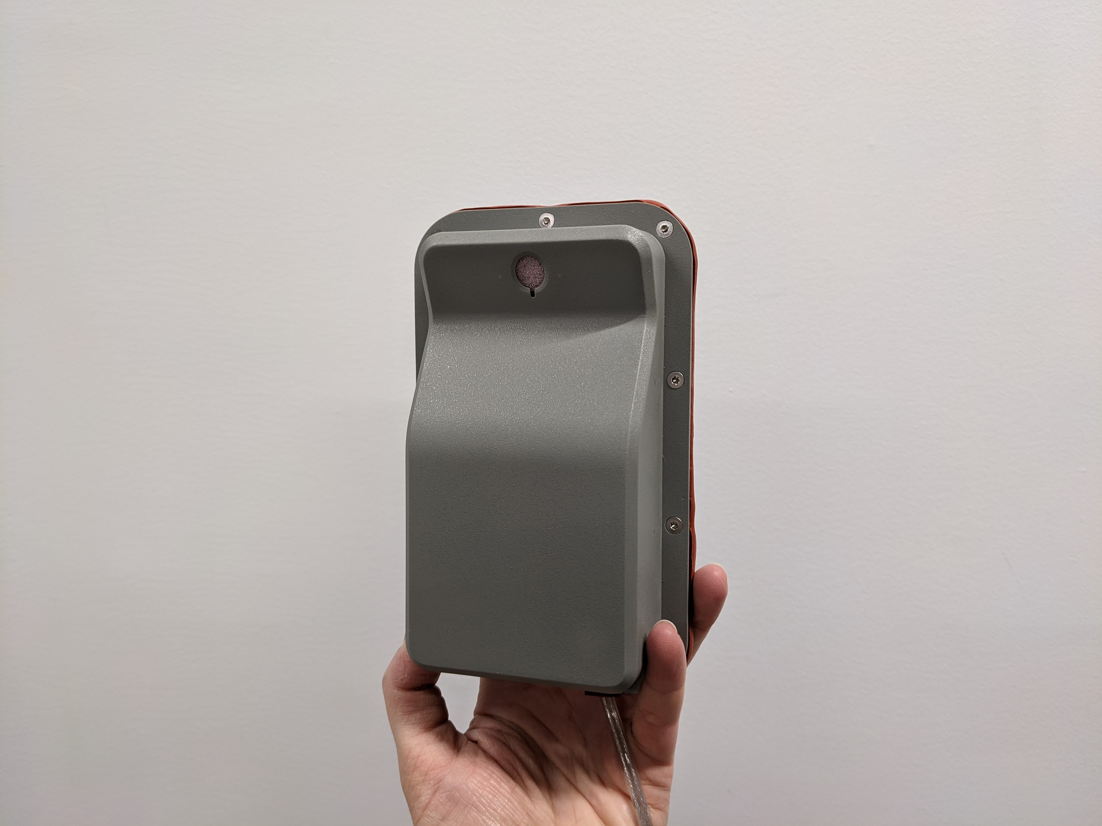
Hardware/History/Assembly Photos/PXL_20201028_211705205.jpg
