sonyc-project/SONYC-Home/Hardware/History/Assembly Photos/PXL_20201028_211718532.jpg

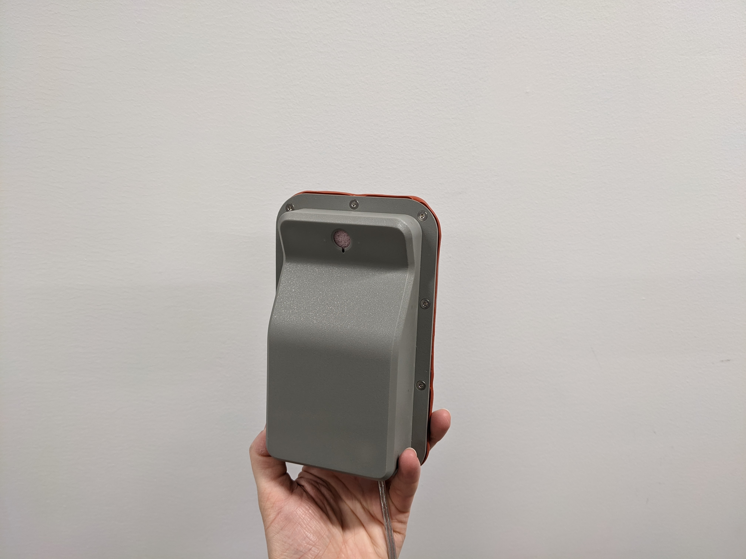
Hardware/History/Assembly Photos/PXL_20201028_211718532.jpg
