sonyc-project/SONYC-Home/Hardware/History/Assembly Photos/PXL_20201028_211719855.jpg

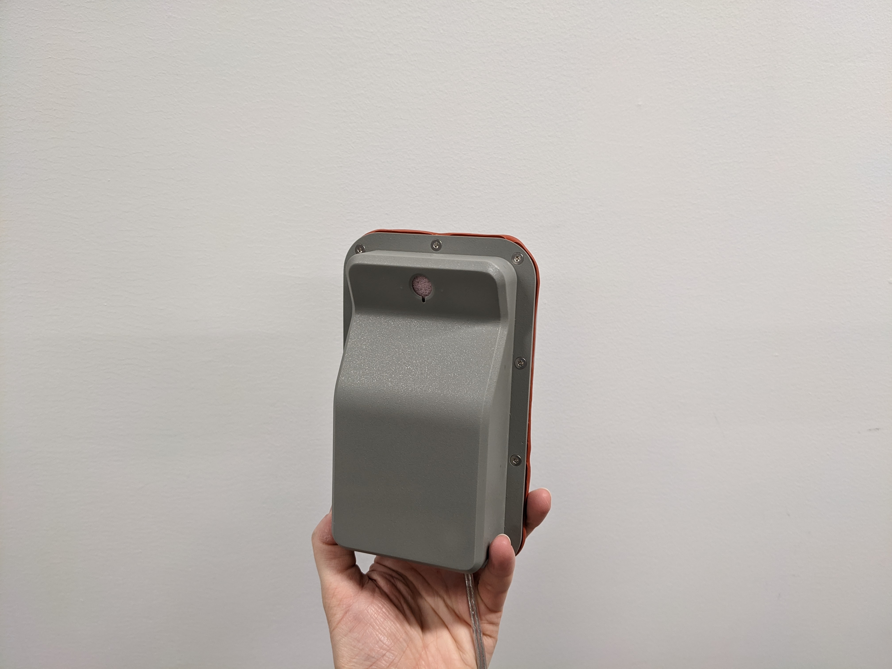
Hardware/History/Assembly Photos/PXL_20201028_211719855.jpg
