sonyc-project/SONYC-Home/Hardware/History/Assembly Photos/PXL_20201028_211740122.jpg

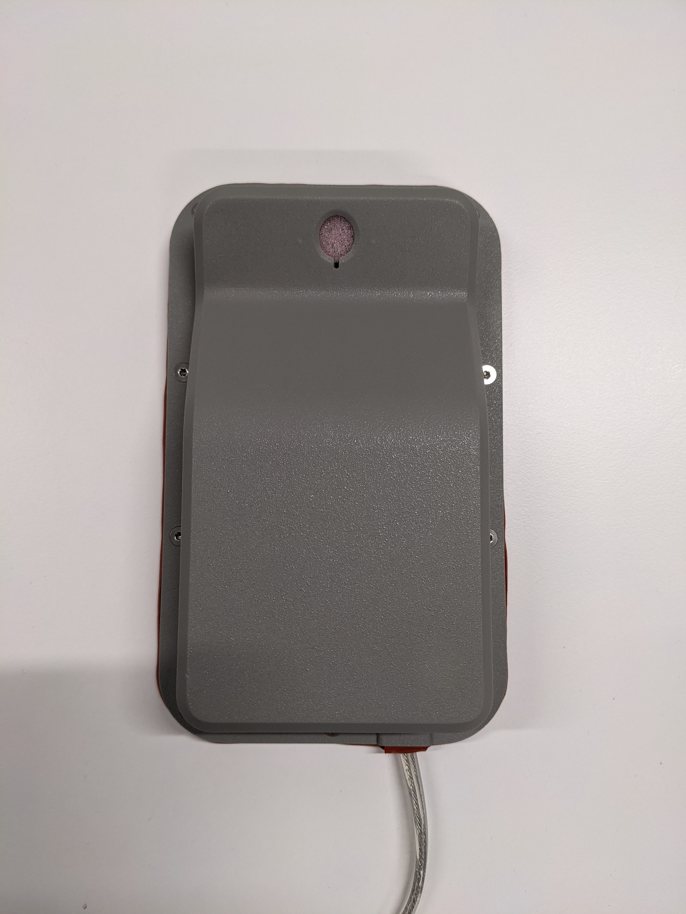
Hardware/History/Assembly Photos/PXL_20201028_211740122.jpg
