sonyc-project/SONYC-Home/Hardware/History/Assembly Photos/PXL_20201028_211753265.jpg

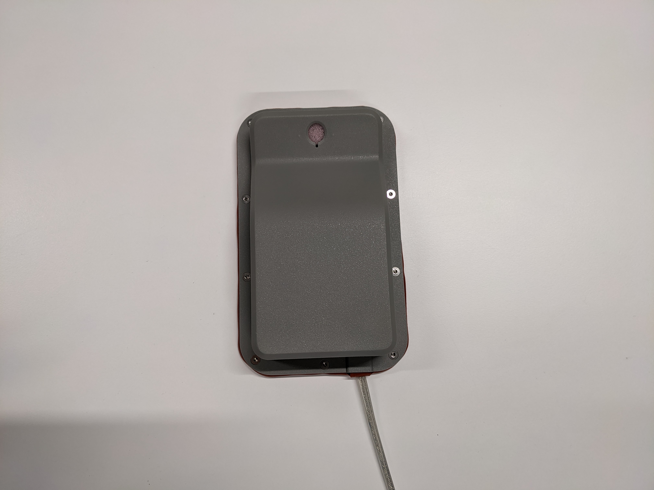
Hardware/History/Assembly Photos/PXL_20201028_211753265.jpg
