sonyc-project/SONYC-Home/Hardware/History/Assembly Photos/PXL_20201028_211756551.jpg

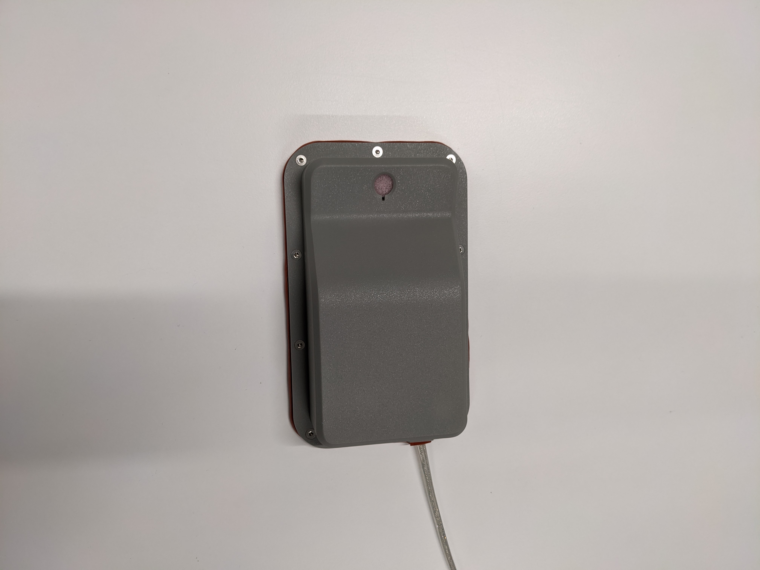
Hardware/History/Assembly Photos/PXL_20201028_211756551.jpg
