sonyc-project/SONYC-Home/Hardware/History/Assembly Photos/PXL_20201028_211807744.jpg

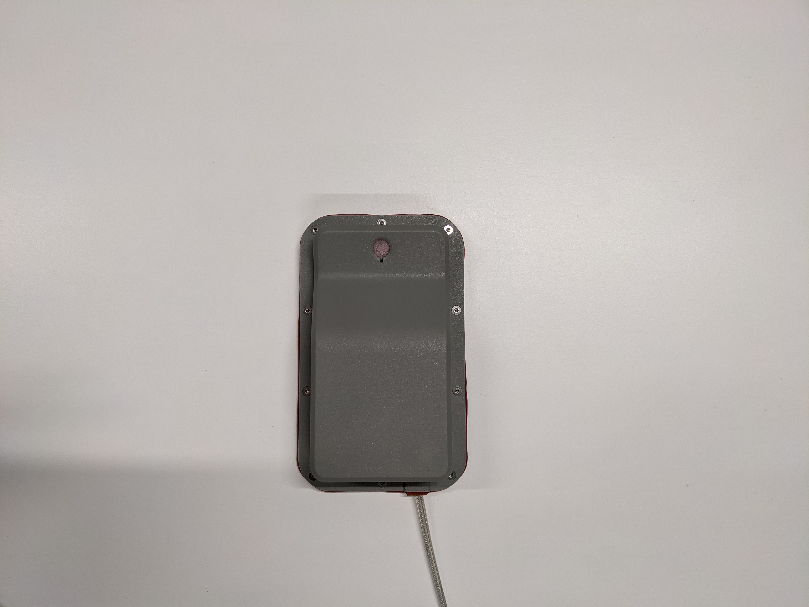
Hardware/History/Assembly Photos/PXL_20201028_211807744.jpg
