sonyc-project/SONYC-Home/Hardware/History/Assembly Photos/IMG_3660.jpeg

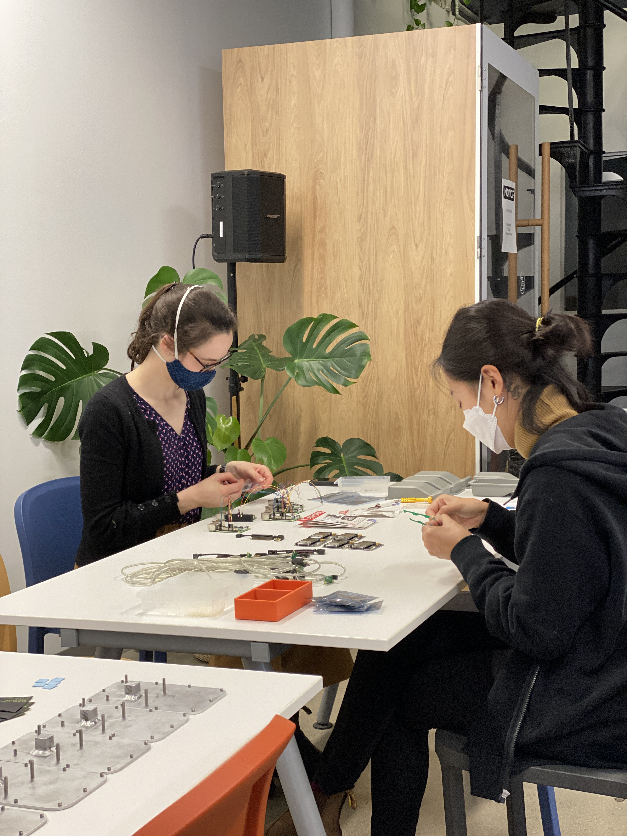
Hardware/History/Assembly Photos/IMG_3660.jpeg
