sonyc-project/SONYC-Home/Hardware/History/Assembly Photos/IMG_3661.jpeg

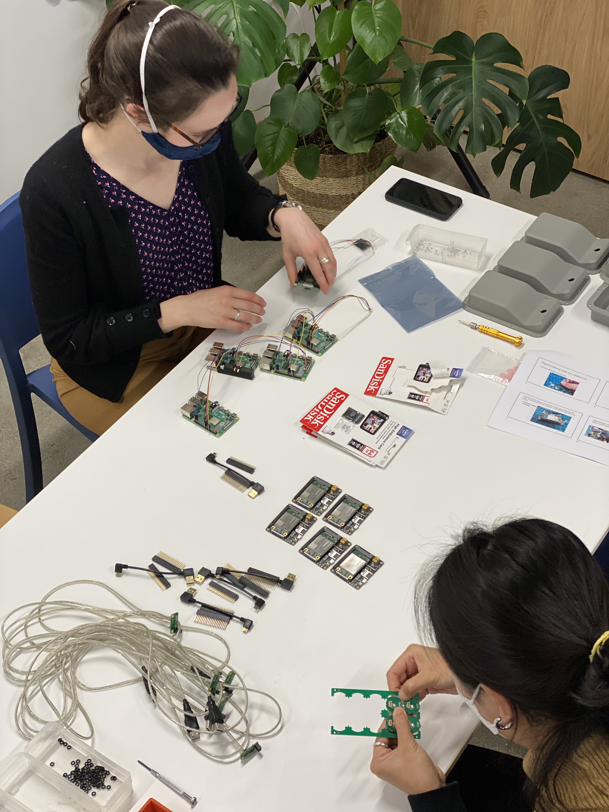
Hardware/History/Assembly Photos/IMG_3661.jpeg
