sonyc-project/SONYC-Home/Hardware/History/Assembly Photos/IMG_3669.jpeg

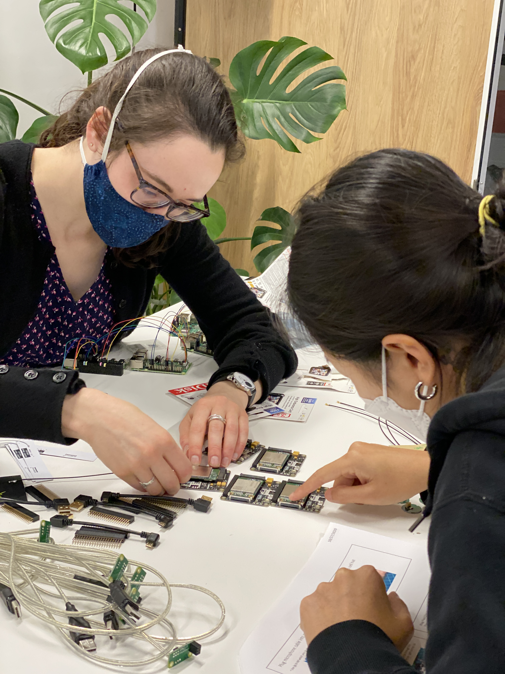
Hardware/History/Assembly Photos/IMG_3669.jpeg
