sonyc-project/SONYC-Home/Hardware/History/Assembly Photos/IMG_3670.jpeg

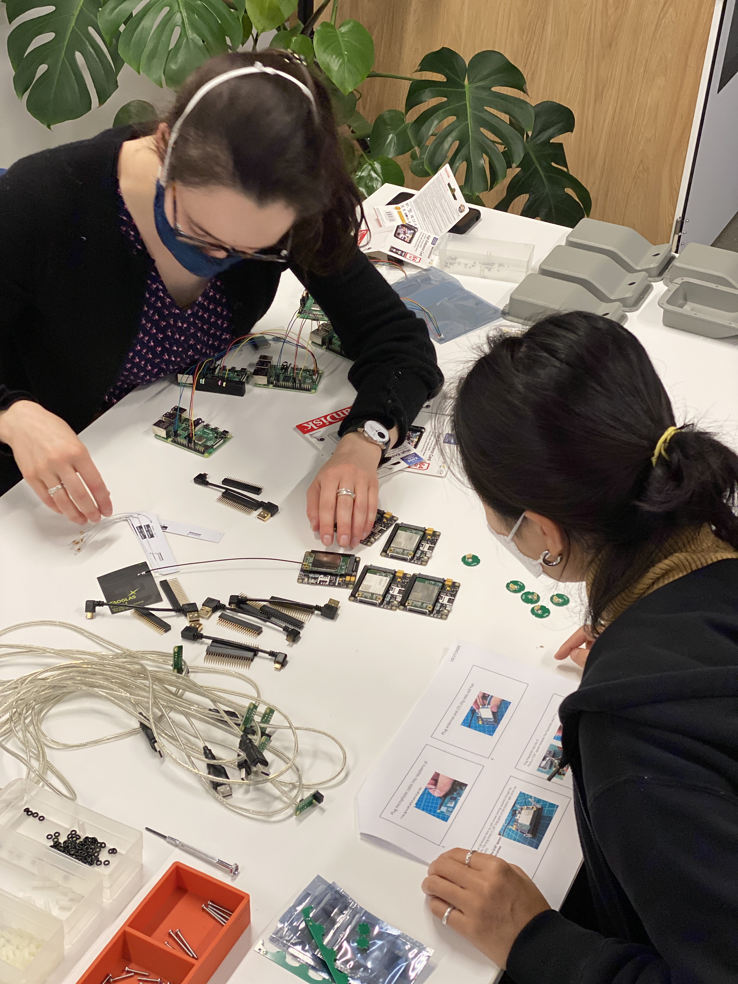
Hardware/History/Assembly Photos/IMG_3670.jpeg
