sonyc-project/SONYC-Home/Hardware/History/Assembly Photos/IMG_3673.jpeg

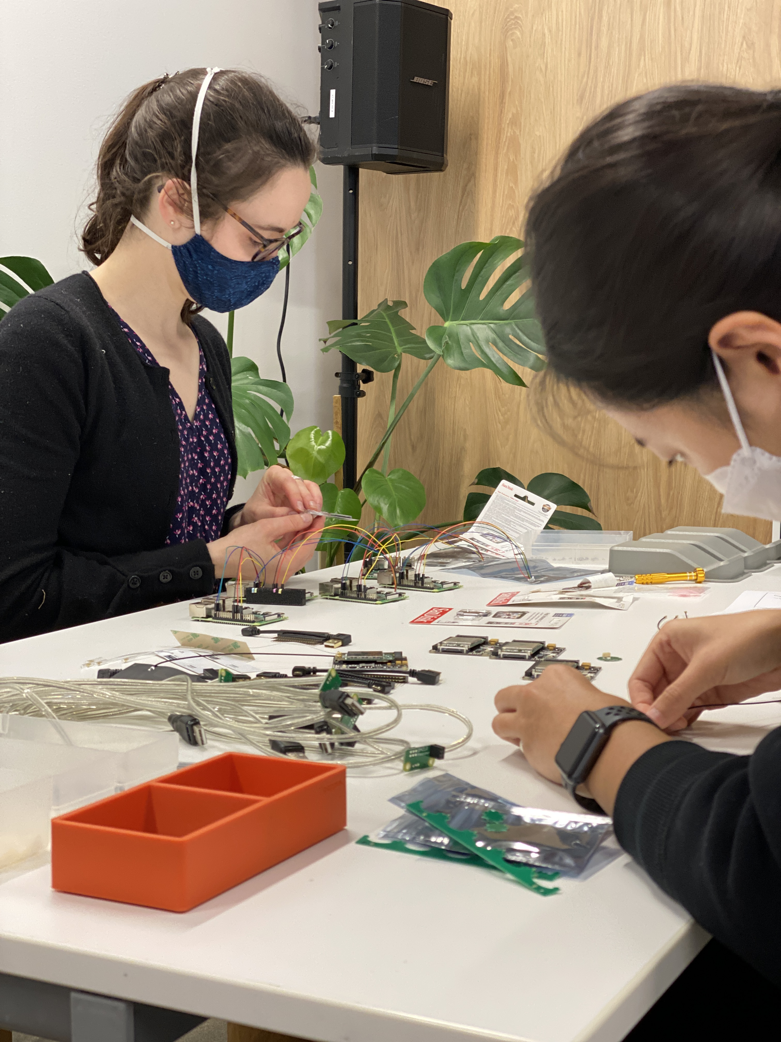
Hardware/History/Assembly Photos/IMG_3673.jpeg
