sonyc-project/SONYC-Home/Hardware/History/Assembly Photos/IMG_3675.jpeg

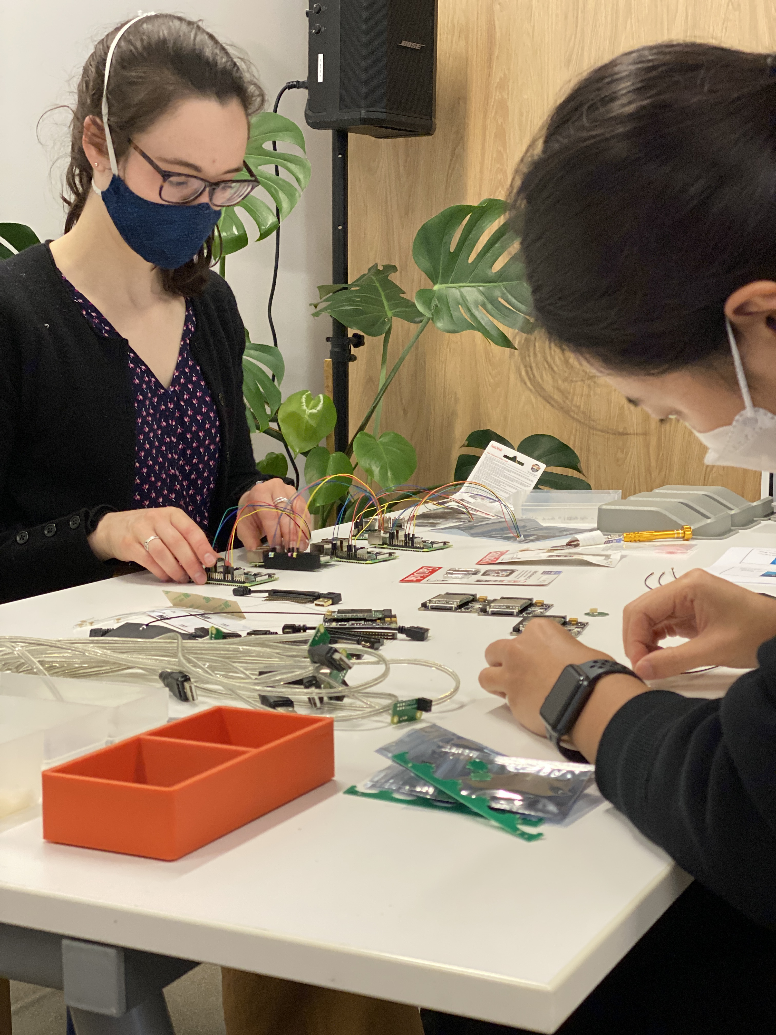
Hardware/History/Assembly Photos/IMG_3675.jpeg
