sonyc-project/SONYC-Home/Hardware/History/Assembly Photos/IMG_3676.jpeg

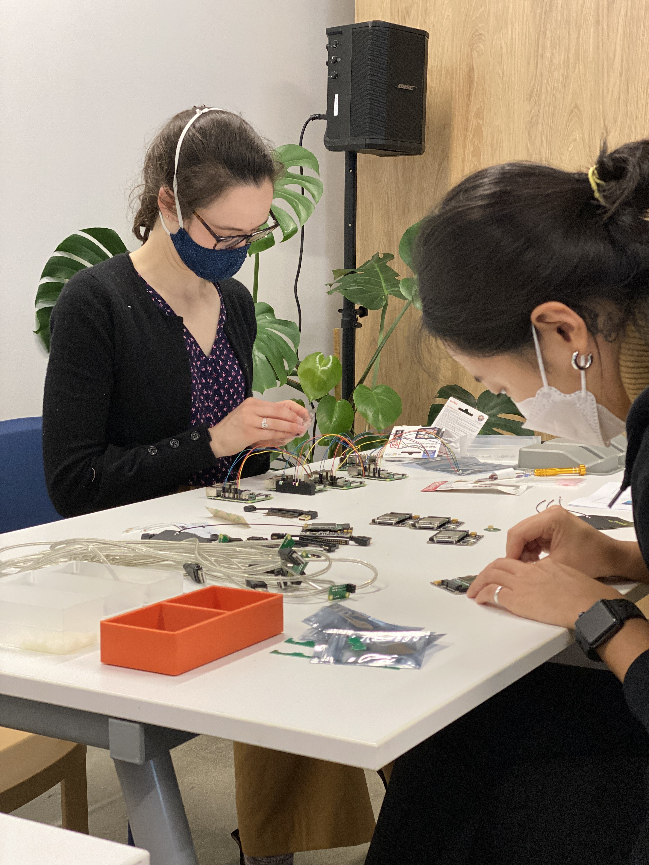
Hardware/History/Assembly Photos/IMG_3676.jpeg
