sonyc-project/SONYC-Home/Hardware/History/Assembly Photos/IMG_3677.jpeg

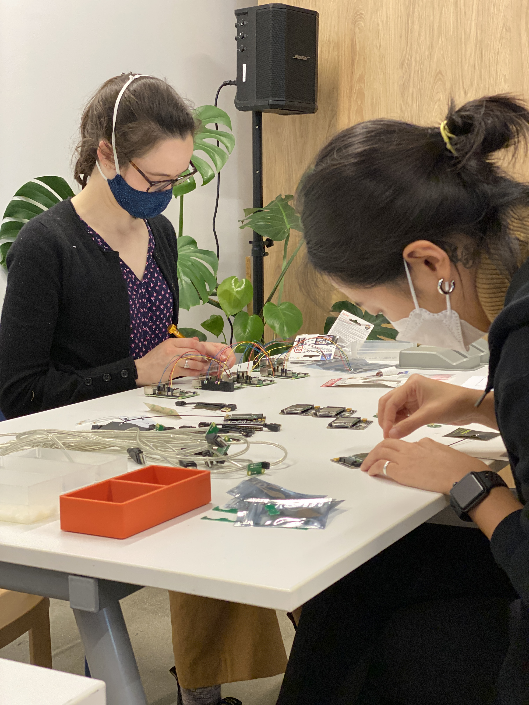
Hardware/History/Assembly Photos/IMG_3677.jpeg
