sonyc-project/SONYC-Home/Hardware/History/Assembly Photos/IMG_3678.jpeg

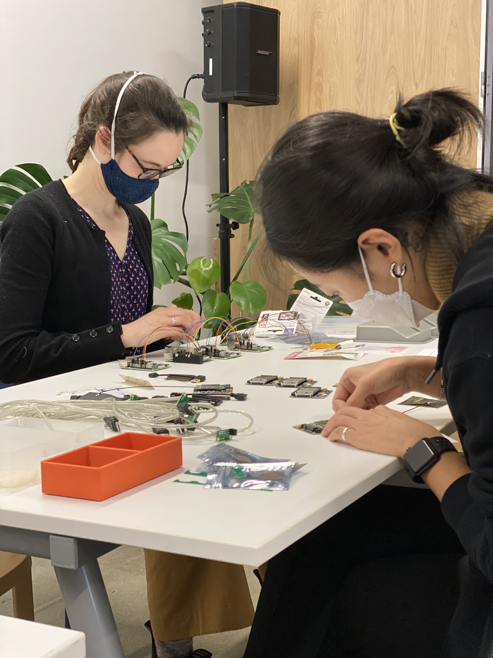
Hardware/History/Assembly Photos/IMG_3678.jpeg
