sonyc-project/SONYC-Home/Hardware/History/Assembly Photos/PXL_20201026_215918843.NIGHT.jpg

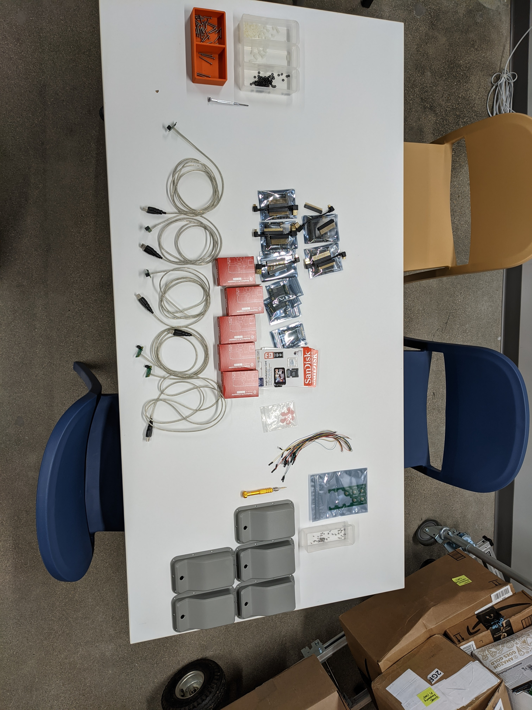
Hardware/History/Assembly Photos/PXL_20201026_215918843.NIGHT.jpg
